ahmadexp/Open-Source-PC110/Discovery/Bowman/readme.md

# U21 "Bowman" — Detailed Analysis

*Source: `Mainboard.pdf` ("PC110 Motherboard", KiCad / Eeschema‑PDF, created 2025‑07‑20), part of the [Open‑Source‑PC110](https://github.com/ahmadexp/Open-Source-PC110) reverse‑engineering project.*

---

## 1. Summary

**U21 (value field: `Bowman`)** is the IBM PC110's **main system‑controller ASIC** — a ~144‑pin custom gate array that bridges the 80486SX CPU local bus to a 16‑bit ISA‑style system bus and absorbs nearly all of the machine's glue logic (ROM decode, interrupt aggregation, DMA handshaking, floppy, keyboard‑MCU link, audio glue and power sequencing).

This corresponds to the documented **custom RIOS chip that "controlled the ISA bus and expanded the bus width to 16 bits."** The PC110 was co‑developed by **IBM Japan and Ricoh (RIOS)** in 1995; its 486SX‑33 CPU and several support chips carry RIOS markings. `Bowman` is the project/codename used on the schematic — there is no public datasheet for the part.
The package is in fact **laser‑marked `RIOS BOWMAN 63G33 1017 JAPAN S536AAI`** (144‑QFP; see the close‑up
in [Chipset/ML-bus-payload-probe.md](../Chipset/ML-bus-payload-probe.md)) — so "BOWMAN" is a genuine part
marking, carrying an IBM `63G33`‑series part number and a `S536AAI` date/lot code, not merely a schematic codename.

| Attribute | Value |
|---|---|
| Reference designator | **U21** |
| Value / codename | **Bowman** |
| Function | System controller / CPU‑to‑ISA bridge ("chipset") |
| Pin count | 144 (highest pin = 144; QFP‑class custom gate array) |
| CPU interface | 80486SX local bus (U76, 80486SX‑33, BGA256) |
| Companion controller | U35 **"Pluto"** (linked via `Bowman_IO1/2`, `Pluto_IO`) |

---

## 2. Role in the system architecture

The PC110 is built around a small set of custom RIOS chips rather than an off‑the‑shelf chipset. Bowman is the heart of that arrangement:

```
   80486SX-33 (U76, BGA256)
        │  CPUA2..25, CPU_ADS#/MIO#/DC#/WR#/RDY#/INTR/RESET, CPUCLK
        ▼
   ┌─────────────┐    M38_IO1..12     ┌──────────────┐
   │  U21 BOWMAN │◄──────────────────►│ U67 M38813M4 │ keyboard / PM MCU
   │  (system    │                    └──────────────┘
   │  controller)│    ESS_IRQ/DACK    ┌──────────────┐
   │             │◄──────────────────►│ ES488 audio  │ (Sound Blaster)
   │             │    ROMA/ROMCE#     ┌──────────────┐
   │             │◄──────────────────►│ Flash BIOS   │
   │             │    Pluto_IO,       └──────────────┘
   │             │    Chipset_IO      ┌──────────────┐
   │             │◄──────────────────►│ U35 PLUTO    │ I/O controller
   └─────┬───────┘                    └──────────────┘
         │ SA0..15 / SD0..7 / IOR#/IOW#/AEN / IRQ2..15 / DRQ/DACK
         ▼
   16-bit ISA-style system bus  → CompactFlash, PCMCIA, YM3812 (OPL2), etc.
```

In short, the CPU talks only to Bowman on its fast local bus; Bowman translates those cycles into 16‑bit ISA bus cycles and routes interrupts, DMA, ROM and peripheral chip‑selects. The companion chip **Pluto (U35)** handles the lower‑speed/peripheral I/O (CF/dock detect, LCD, IrDA, RS‑232 enable, floppy data lines, keyboard speaker, RAM ID, BIOS write‑enable), and the two custom chips exchange status over dedicated `Bowman_IO`/`Pluto_IO` lines.

---

## 3. Complete pinout (by function)

### 3.1 CPU local bus — 80486SX interface (left side of symbol)

| Signal | Pin | Notes |
|---|---|---|
| `CPUA2`–`CPUA25` | 10‑17, 19‑27, 29‑35 | CPU address bus (A0/A1 handled as byte‑enables, not exposed here) |
| `CPU_ADS#` | 49 | Address strobe (486 ADS#) |
| `CPU_MIO#` | 50 | Memory / IO# (486 M/IO#) |
| `CPU_DC#` | 41 | Data / Control# (486 D/C#) |
| `CPU_WR#` | 42 | Write / Read# (486 W/R#) |
| `CPU_RDY#` | 134 | Ready / cycle complete (486 RDY#) |
| `CPU_INTR` | 133 | Maskable interrupt to CPU (8259 INTR equivalent) |
| `CPU_RESET` | 46 | CPU reset |
| `CPUCLK` | 38 | CPU clock |

### 3.2 16‑bit ISA‑style system bus

| Signal | Pin | Notes |
|---|---|---|
| `SA0`–`SA15` | 55‑63, 65‑71 | System address bus |
| `SD0`–`SD7` | 96,95,94,93,92,91,89,88 | System data (low byte on Bowman; high byte routed elsewhere) |
| `IOR#` | 112 | I/O read |
| `IOW#` | 113 | I/O write |
| `AEN` | 114 | Address enable (DMA in progress) |
| `MEMCS16#` | 119 | 16‑bit memory chip‑select |
| `LDEV#` | 43 | Local device select |
| `ADDHI` | 124 | High‑address qualifier |
| `DS3#` | 123 | Decode/strobe |

### 3.3 Interrupt controller (8259‑class aggregation)

| Signal | Pin | | Signal | Pin |
|---|---|---|---|---|
| `IRQ2` | 87 | | `IRQ10` | 78 |
| `IRQ3` | 85 | | `IRQ11` | 77 |
| `IRQ4` | 84 | | `IRQ12` | 76 |
| `IRQ5` | 83 | | `IRQ14` | 75 |
| `IRQ7` | 81 | | `IRQ15` | 74 |
| `IRQ9` | 79 | | `KB_IRQ1` | 86 (keyboard IRQ1) |
| `ESS_IRQ1` | 118 | | | |

### 3.4 DMA & floppy

| Signal | Pin | Notes |
|---|---|---|
| `FINTR` | 82 | Floppy interrupt |
| `FDRQ` | 115 | Floppy DMA request |
| `PDRQ` | 117 | Peripheral DMA request |
| `DACK#` | 120 | DMA acknowledge |
| `PDACK#` | 121 | Peripheral DMA acknowledge |
| `ESS_DACK#` | 122 | Audio (ESS) DMA acknowledge |
| `FDD_IO` | 125 | Floppy control I/O |

### 3.5 ROM / BIOS decode

| Signal | Pin | Notes |
|---|---|---|
| `ROMA12`–`ROMA19` | 9,7,6,5,4,3,2,143 | ROM high address lines |
| `ROMCE#` | 142 | ROM chip‑enable |

### 3.6 Keyboard / power‑management MCU (U67 = Mitsubishi M38813M4) — mapped from the schematic

> **Correction (2026‑07, from the U67 schematic sheet + KBC firmware):** the earlier claim that
> `M38_IO1..12` is a "parallel link to U67" is **wrong**. Read directly from the U67 schematic
> (`Components/U67-M38813E4HP/M38813M4.png`, IC79 = M38813 M4‑084HP, TQFP‑64), **U67 has no `M38_IO`
> pins at all.** Its entire host interface is a **classic 8042‑style keyboard‑controller bus** on the
> shared system `SD`/control lines. The `M38_IO1..12` nets on Bowman pins 97,98,101–107,110,111,139
> therefore do **not** reach U67. **A deterministic wire trace of `ASIC.kicad_sch` confirms the far end
> is U6 (the M38223 power MCU):** Bowman pins 106/107/110/111 carry U6's own port nets `M38_P15_Buf`,
> `M38_P14_Buf`, `M38_P43`, `M38_P41` (P14/P15 buffered en route; all present on U6's sheet
> `Power.kicad_sch`). So `M38_IO*` is a **narrow ~4‑line control/handshake link from U6 to Bowman**: only U6 pins P14, P15
> (buffered), P41, P43 actually reach Bowman (106/107/110/111) — the other `M38_IO` symbol pins (97–105)
> are unconnected stubs and pin 139/"IO13" is a power tie (R349→PNET1) in this schematic. So despite the
> "IO1..13" pin names it is **not** a byte‑wide bus, and **not** the `0xEC/0xED` path — that window is the
> VL82C420 chipset shadow/cache/ROM config bank ([Chipset §13j.5](../Chipset/readme.md)). U6's own
> battery/power telemetry leaves U6 over its SIO1 **serial** (→ U72 = HD151015), surfaced to software via
> APM `INT 15h 530A`. **[C]**

**U67 ↔ Bowman / Pluto — the real links** (net names from the U67 schematic; gate‑array pin numbers
from the ES488 netlist, `Discovery/ES488/mainboard.txt`):

| Signal | U67 pin (port) | Dir | Bowman pin | Pluto pin | Function | Conf |
|---|---|---|---|---|---|---|
| `SD0`–`SD7` | 3,2,1,64,63,62,61,60 (DQ0‑7) | I/O | shared SD bus | shared SD bus | 8‑bit host/system data bus (DBB) | **[C]** |
| `IOW#` | 4 (W#) | in | 113 | 89 | host I/O write strobe | [C] net / [H] pins |
| `IOR#` | 5 (R#) | in | 112 | 86 | host I/O read strobe | [C] net / [H] pins |
| `KBCCS#` | 6 (S#) | in | — | 60 | KBC chip‑select (Pluto decodes the I/O port) | **[C]** |
| `SA[2]` (A0) | 7 (A0) | in | — | — | register / command‑vs‑data select (ISA A2) | **[C]** |
| `IRQ1` | 15 (P44) | out | 86 | — | keyboard interrupt to host | **[C]** |
| `IRQ12` | 14 (P45) | out | 76 | — | mouse/aux interrupt to host | **[C]** |
| `KB_CNTR#` | 59 (P60/CNTR#) | — | — | 61 | control/counter line to Pluto (via R494) | [C] net / [H] dir |
| `SPKUP` | 29 (P23) | out | — | 44 | speaker drive (up) | **[C]** |
| `SPKDN` | 30 (P22) | out | — | 43 | speaker drive (down) | **[C]** |
| `RESET#` (`RSTDRV#`) | 19 | in | 48 | 66 | system reset (multi‑drop, from IC106) | **[C]** |
| `KBRST#` | 10 (P51/TXD) | out | (sheet 009) | — | KBC→CPU fast reset (8042 output) | **[C]** |
| `A20G` | 11 (P50/RXD) | out | (sheet 009) | — | A20 gate (8042 output) | **[C]** |

`KB_SCRLED#` on **Bowman 53** is *not* U67's scroll‑lock LED: the schematic shows U67's `SCRLED#`
(pin 25) going to the LED sub‑board (sheet 023), so Bowman‑53's net is a separate/derived signal. **[H]**

**Full U67 (M38813M4) pinout** and the 8042 host protocol are documented in the Pluto readme
(§ "M38813 keyboard/PM MCU — full pinout"), since Pluto is the chip that chip‑selects and gates it.

### 3.7 Power, clocks & housekeeping

| Signal | Pin | Notes |
|---|---|---|
| `PWRGD_IN` | 141 | Power‑good input from PSU |
| `PWRGD` | 47 | Power‑good output / system ready |
| `PSU_IO1` / `PSU_IO2` | 131 / 138 | Power‑supply control I/O |
| `24MHz` | 40 | 24 MHz reference clock |
| `32kHz` | 51 | 32.768 kHz timekeeping clock |
| `VolUP` / `VolDN` | 127 / 128 | Volume button inputs |
| `Pluto_IO` | 129 | Link to U35 (Pluto) |
| `Chipset_IO1`–`5` | 45,140,39,52,130 | **VL82C420↔Bowman ML bus** (measured live 2026-07-06, pin IDs corrected 2026-07-14, see [Chipset §11b](../Chipset/readme.md)): `Chipset_IO3`/pin 39 = **MLCLK** (~22.7 MHz), `Chipset_IO4`/pin 52 = **MLADS#**; `Chipset_IO1/2/5` (45/140/130) idle = **MLRDY#/MLLBA#/MPriority** (adopted naming, in KiCad; cache-less / fixed-timing) |

### 3.8 Power rails

| Rail | Pins |
|---|---|
| `VCC` / `VCC2` | 1, 18, 36, 37, 54, 72, 73, 90, 99, 108, 109, 126, 144 |
| `GND` | 8, 28, 44, 64, 80, 100, 116, 136 |
| `NC` (no connect) | 132, 135, 137 |

---

## 4. Surrounding components and the chips Bowman talks to

| Ref | Part | Role | Link to Bowman |
|---|---|---|---|
| **U76** | 80486SX‑33 (BGA256) | Main CPU (Intel SL‑Enhanced, RIOS‑marked) | CPU local bus + control |
| **U35** | **Pluto** (custom, ~100‑pin) | Peripheral I/O controller (CF/dock/LCD/IrDA/RS‑232, FDD data, KB speaker, RAM ID, BIOS WE) | `Bowman_IO1/2`, `Pluto_IO`, shared SA/SD bus |
| **U67** | M38813 / M38813M4 | Mitsubishi 740‑family keyboard MCU (8042‑style KBC) | 8042 host bus (`SD0‑7`,`IOR#`/`IOW#`,`KBCCS#`,`SA2`), `IRQ1`(pin15→B86), `IRQ12`(pin14→B76), `RESET#`(19). **NOT** `M38_IO*` (see §3.6) |
| **U10** | YM3812 (OPL2) + YM3014B DAC | Yamaha FM synthesis | via ISA bus |
| — | ES488 / ES488F | ESS AudioDrive (Sound‑Blaster‑compatible) | `ESS_IRQ1`, `ESS_DACK#` |
| — | Flash BIOS ROM | System firmware | `ROMA*`, `ROMCE#` |
| **J11** | CompactFlash | Mass storage (16‑bit `SD0..15`) | via ISA bus |
| **U70** | TPS2201 | PCMCIA dual‑slot power switch (near U21) | PSU / PNET nets |
| **U30A** | 74LVT74 | Flip‑flop / reset timing near U21 | PNET nets |

Local support around U21 on the sheet includes pull‑ups `R98` (4.7k) / `R99` (470Ω), transistors `Q9` / `Q13`, and the `PNET`/`PSU_IO` power‑sequencing network shared with the PCMCIA power switch — consistent with Bowman also overseeing card‑slot power‑up and reset timing.

---

## 5. Observations & open questions for the project

1. **No `CPUA0`/`CPUA1`.** The CPU address bus to Bowman starts at A2; byte selection is presumably handled via byte‑enable signals (standard for the 486 bus). Worth confirming which pins carry BE# if any.
2. **8‑bit data on Bowman, 16‑bit elsewhere.** Bowman exposes only `SD0..7`, yet the documented job of the RIOS chip is the **16‑bit** bus expansion (CompactFlash uses `SD0..15`). The high byte / `MEMCS16#` steering likely happens through `ADDHI`, `Chipset_IO*`, or in concert with Pluto — a good thing to trace against the X‑rays.
3. **Bowman ↔ Pluto coupling (traced 2026‑07).** The dedicated inter‑gate‑array link is a **single
   point‑to‑point line**: Bowman **pin 129 `Pluto_IO`** ↔ Pluto **pin 51 `Bowman_IO1`** (direct, no series
   R). Pluto's **pin 52 `Bowman_IO2`** is **not wired to Bowman** — it dead‑ends on the ASIC sheet
   (effectively NC/spare; the earlier "R85" note is unverified — R85 is absent from `ASIC.kicad_sch`).
   Beyond that one wire the two chips share only standard ISA/system control: `AEN` (U21‑114↔U35‑6),
   `IOR#` (112↔86), `IOW#` (113↔89), `KB_RESET#` (48↔66), `PWRGD` (47↔67). The lone `Pluto_IO`/`Bowman_IO1`
   line is an inter‑gate‑array **status/handshake** signal; its direction and protocol aren't determinable
   from connectivity alone (one wire, no software‑visible register — would need a live bus probe). **[C]**
   connectivity / **[H]** function.
4. **Codenames.** ~~`Bowman` and `Pluto` appear to be project codenames rather than IBM/RIOS part markings.~~ **Partly resolved (2026-07-14):** the Bowman package is laser‑marked `RIOS BOWMAN 63G33 1017 JAPAN S536AAI`, so `BOWMAN` *is* the real part marking (IBM `63G33`‑series P/N). Whether `Pluto` is likewise marked on U35 is still open.

### Live probe (2026) — Bowman has no host-readable config bank ✅ **[RE]**
Bowman is the **transparent 486↔ISA bridge**: unlike the VL82C420 (which has an indexed config space
now dumped — see [Chipset §13a](../Chipset/)) and Pluto (whose FDC/PCIC/EC windows are readable — see
[Pluto §6c](../Pluto/)), Bowman does **not** expose a host-visible register bank. Live probing on a
running unit found the two candidate config-pair banks the BIOS helper table can reach —
`0x24/0x25` and `0xD00/0xD01` — read back **all-`0xFF`** on this machine (even with the `0x22/0x23`
config gate open), and the `0x4F` config latch Bowman/SCAMP shares is **write-only** (147 POST writes,
zero reads; indices `0x11,0x66,0x70,0x0A,0x1E,0xB6,0x8F,0x65,0xBF,0xFF`). So Bowman's bridge/decode
behaviour is configured at POST and is not read-back-able at runtime — consistent with a hard-wired
gate array rather than a programmable controller with a live register file.

---

---

## 6. Discovery from the ROM dump — U36 font ROM (`MSM538032E@SOP44.BIN`)

A binary dump was supplied as "from U28," but U28 in the schematic is DRAM (`M5M4V16160BTP`). The dump actually belongs to **U36**, the OKI **`MSM538032E`** mask ROM (alt. marking `M538032C`, SOP‑44, 16‑bit `D0..D15`, `A0..A19`, `CE#`/`OE#`/`BHE`, on the `OKI_SA*` / `SD[0..15]` nets). Its address/select interface **is** Bowman's `ROMA*`/`ROMCE#` bus (see "How the CPU reads it" below); the **BIOS flash** (U59, 28F002) is decoded *separately* by the **chipset** (`Chipset_BIOS_CE#`), so the two ROMs do **not** share a chip‑select. This is a CPU‑addressable **font ROM** on the system data bus.

### What the dump contains

- **Header:** magic `55 AA 10 CB`, label `FONT`, and the string
  `84G7940 (C) Copyright IBM Corporation 1990, 1995 All Rights Reserved`, dated **03/23/95**.
- **IBM part number 84G7940** — the PC110 **DOS/V display font ROM**.
- Size **1 MiB**; the file is fully populated (the seven font regions account for ~1 MB).

### Font directory (parsed from offset 0x210; 48‑byte entries)

| Font set | Glyph size | Bytes/glyph | Data offset | Glyphs |
|---|---|---|---|---|
| System SBCS 12 | 6 × 12 | 12 | 0x0D8000 | 256 |
| System SBCS 16 | 8 × 16 | 16 | 0x002000 | 256 |
| System SBCS 19 | 8 × 19 | 19 | 0x000400 | ~256 |
| System SBCS 24 | 12 × 24 | 48 | 0x044000 | 256 |
| System DBCS 12 | 12 × 12 | 18 | 0x0D8C00 | ~8,900 |
| System DBCS 16 | 16 × 16 | 32 | 0x003000 | ~8,300 |
| System DBCS 24 | 24 × 24 | 72 | 0x047000 | ~8,200 |

- **SBCS = single‑byte (ANK), JIS X 0201:** ASCII (with `¥` at 0x5C instead of backslash) plus half‑width katakana at 0xA1–0xDF. Rendering glyph 0x41/0x42 produces a clean "A"/"B" — confirmed.
- **DBCS = double‑byte, JIS X 0208:** hiragana, full‑width katakana, Greek, Cyrillic, symbols, and the ~6,800 kanji of JIS levels 1 & 2. Rendered glyph blocks show correct kana/Greek/Cyrillic.

### Why it matters

The PC110 has no hardware kanji video; **IBM DOS/V renders Japanese text in software by reading bitmaps from this ROM.** Four pixel heights (12/16/19/24) supply screen text, larger UI, and print‑quality glyphs. Decoding the directory format means the entire glyph set can now be extracted, documented, and cross‑checked — useful for a full BOM entry on U36 and for anyone re‑implementing the font path (e.g., in an FPGA or emulator).

Render proofs: `font_SBCS16_ascii.png` (single‑byte set) and `font_DBCS16_kanji.png` (double‑byte kana/Greek/Cyrillic block).

### How the CPU reads it — decode & paging  ✅ **[C, from `ROM.kicad_sch` + datasheet]**

Traced deterministically from `PCB/Mainboard/ROM.kicad_sch`:

| U36 pins | Net | Source |
|---|---|---|
| A0–A11 (low addr) | `SA1`–`SA12` | **direct ISA system address** — the access *window* |
| A12–A19 (high addr) | `OKI_SA12`–`OKI_SA19` = Bowman `ROMA12`–`ROMA19` | **Bowman page latch** (8 bits) |
| CE# | `OKI_CE#` = Bowman `ROMCE#` (pin 142) | Bowman address decode |
| OE# | `MEMR#` | ISA memory‑read → a **memory** window, not I/O |

So the 1 MiB font ROM is a **paged, memory‑mapped ROM controlled by Bowman**: the CPU sees a small window
addressed directly by the ISA bus (`SA1–SA12`), and Bowman supplies the upper address (page) via its
`ROMA12–19` latch — the CPU selects a page by writing a Bowman register, then reads glyph data from the
window. **Page 0 is an 8 KB option‑ROM window** (the `55 AA 10 CB` header at offset 0, size byte `0x10` =
8192 bytes, checksum‑valid) — exactly the `SA1–SA12` span, and the DOS/V font driver's entry point.

**This corrects §6's opening (and §3.5):** Bowman's `ROMA*`/`ROMCE#` drives the **font ROM (U36)**, *not*
the BIOS flash. The BIOS flash (U59, 28F002BX) is a **chipset‑decoded** path (`Chipset_BIOS_CE#`,
`Chipset_SA16`, `BIOS_SA17`, `OE#=MEMR#`) — a separate select; the two ROMs never share a chip‑enable.

### Open items — resolved
- **Second bank? No.** The MSM538032E is an **8‑Mbit (1 MiB)** part — 512 K × 16 / 1 M × 8 (datasheet
  `Datasheets/top/MSM538032C.pdf`; analysis report: "8‑Mbit mask ROM, 1 MiB as x8"). The 1 MiB dump is the
  **complete device** — no second bank. (The earlier "~2 MB / A0–A19×16" worry assumed word‑wide use of
  all 20 lines; the device is 8 Mbit.)
- **`OKI_SA*`/`OKI_CE#` decode: mapped above** — Bowman‑paged, memory‑mapped (`ROMA12–19` page latch +
  `SA1–12` window + `ROMCE#`/`MEMR#`).

---

## Sources

- Uploaded schematic: `Mainboard.pdf` ("PC110 Motherboard", KiCad).
- Uploaded ROM dump: `MSM538032E@SOP44.BIN` (IBM font ROM P/N 84G7940, 1995).
- [Open‑Source‑PC110 (GitHub) — ahmadexp](https://github.com/ahmadexp/Open-Source-PC110)
- [Reverse Engineering The IBM PC110, One PCB At A Time — Hackaday](https://hackaday.com/2025/04/06/reverse-engineering-the-ibm-pc110-one-pcb-at-a-time/)
- [IBM PalmTop PC110 teardown — iPhone Wired](https://iphonewired.com/news/11094/) (CPU 486SX‑33 BGA with RIOS markings; C&T 65535A graphics; ESS + Yamaha audio; IBM Japan + Ricoh)
- [PC110 — ThinkWiki](https://www.thinkwiki.org/wiki/PC110)
