ahmadexp/Open-Source-PC110/Discovery/Trackpoint/readme.md

# U75 — Trackpad Controller

*PC110 Motherboard · KiCad reverse-engineering project (Open-Source-PC110)*

---

## 1. Summary

**U75** is the **trackpad (pointing-device) controller** on the IBM PC110 motherboard. Instead of a dedicated touch ASIC, the design uses a small general-purpose **4-bit microcontroller** running firmware that scans the capacitive/resistive pad matrix, reads the physical click buttons, and reports pointer movement to the host over a PS/2-style clock + data interface.

| Field | Value |
|---|---|
| Reference designator | **U75** |
| Part number (Value) | **D17137AGT** (NEC µPD17137A) |
| Device class | 4-bit single-chip microcontroller (NEC "17K" / µPD17134A subseries) |
| Footprint | **PC110:SSOP-28** (28-pin shrink small-outline package) |
| Schematic description | "Trackpad Controller" |
| Net-naming prefix | `D171_` (derived from the part number) |
| Source document | `Mainboard.pdf` — *PC110 Motherboard*, generated by KiCad Eeschema |

---

## 2. The part: NEC µPD17137A

`D17137AGT` decodes to NEC's **µPD17137A**, a member of the **µPD17134A subseries** of NEC's **17K-family 4-bit single-chip microcontrollers** (circa early 1990s). The leading `D` is NEC's standard prefix (µPD), and the `GT` suffix denotes the package option.

Key characteristics of the family:

- 4-bit CMOS single-chip microcontroller architecture.
- On-chip ROM/RAM, timer, and general-purpose I/O ports organized into nibble-wide ports (P0A, P0B, P0C, P1A, P1B …).
- Designed for low-cost embedded control tasks — exactly the role it plays here, scanning a pointing-device sensor and emulating a mouse.

Using a programmable MCU (rather than fixed-function silicon) is why the schematic exposes raw port lines (`P0A0`, `P0B1`, etc.) directly to the pad — the scanning logic lives in firmware.

---

## 3. Connections / net map

All I/O nets carry the `D171_` prefix (after the part number). Grouped by function:

### Pad sensing matrix (scan / sense lines)
These read finger position off the trackpad surface.

- **Port 0A:** `/D171_P0A0`, `/D171_P0A1`, `/D171_P0A2`, `/D171_P0A3`
- **Port 0B:** `/D171_P0B0`, `/D171_P0B1`, `/D171_P0B2`, `/D171_P0B3`
- **Port 0C:** `/D171_P0C2`, `/D171_P0C3`
- **Port 1A:** `/D171_P1A0`, `/D171_P1A1`, `/D171_P1A2`, `/D171_P1A3`
- **Port 1B:** `P1B0` (appears as the auto-named net `Net-(U75-P1B0)`)

### Button inputs
- `/TRKPD_Lclick` — left physical click button
- `/TRKPD_Rclick` — right physical click button

### Host interface (pointer data out)
- `/D171_GPCLK` — PS/2-style clock line
- `/D171_GPDATA` — PS/2-style data line

### Control
- `Net-(U75-INT)` — interrupt line

### Power
- **`PNET3`** — supply rail
- **`GND`** — ground

---

## 4. Support circuitry around U75

### Decoupling / bulk capacitors
| Ref | Value | Footprint |
|---|---|---|
| C87 | 120 nF | C_0402_1005Metric |
| C126 | 150 nF | C_0402_1005Metric |
| C135 | 2.7 µF | C_0805_2012Metric |

### Resistors (pull-ups / dividers)
| Ref | Value | Notes |
|---|---|---|
| R196 | 47 k | |
| R197 | 47 k | |
| R198 | 10 k | |
| R200 | 47 k | |
| R201 | 100 k | |
| R203 | 10 k | |
| R204 | 47 k | |
| R205 | 100 k | |
| R206 | 47 k | |
| R199 | DNP | not populated |
| R202 | DNP | not populated |

All resistors use the `R_0402_1005Metric` footprint.

---

## 5. Board neighborhood

U75 sits in a dense region of the motherboard alongside the core system controllers, and the CPU data bus (`/CPU_D28`–`/CPU_D31`) routes nearby.

| Ref | Value | Role | Package |
|---|---|---|---|
| **U51** | CHIPS65535 | Chips & Technologies VGA / LCD controller | BGA-169 |
| **U74** | RB5C396 | Ricoh PC-Card / power controller | BGA-256 |
| **U75** | D17137AGT | Trackpad controller | SSOP-28 |

Other nearby nets observed: `Net-(C135-+)`, `Net-(C281--)`, `Net-(C283-+)`, and power net `PNET3`.

---

## 6. Functional picture

```
                 +-------------------------+
  Pad matrix --->|  P0A0..P0A3             |
  (rows/cols)    |  P0B0..P0B3             |
                 |  P0C2, P0C3             |
                 |  P1A0..P1A3, P1B0       |
                 |                         |
  L/R buttons -->|  TRKPD_Lclick           |---> GPCLK  (PS/2 clock) --> host KBC
                 |  TRKPD_Rclick           |---> GPDATA (PS/2 data)  --> host KBC
                 |                         |
                 |  U75  (NEC uPD17137A)   |---> INT (interrupt)
                 |  SSOP-28, 4-bit MCU     |
                 +-----------+-------------+
                       PNET3 |  | GND
                             |  |
                        decoupling: C87, C126, C135
```

The MCU continuously drives/reads the port lines to scan the pad, debounces the two click inputs, and streams the resulting pointer packets to the system's keyboard/mouse controller over the `GPCLK`/`GPDATA` pair.

---

## 7a. Live probe & firmware-extraction feasibility (2026)  ✅ **[RE]**

**Question asked:** can U75's firmware be dumped *from inside* — i.e. over the running system
([COMrade](../Live-Dump/)), without desoldering/decapping? Investigated live; the short answer is
**no**, and here is exactly why, with on-device evidence.

**U75 is reachable, and it is alive.** Its only host path is the **PS/2 aux channel** through the
8042 keyboard controller (the `GPCLK`/`GPDATA` pair, §3). On a running unit that channel is
**disabled at rest** (8042 command byte `0x65`: aux-disable bit set, IRQ12 off — no mouse driver
loaded at the DOS prompt). Bringing it up (`0xA8`), querying the device, and restoring the byte to
`0x65` afterwards, U75 answers the standard pointing-device protocol perfectly:

| Command | Response | Meaning |
|---|---|---|
| Reset `0xFF` | `FA AA 00` | ACK, **self-test passed (BAT OK)**, device ID `0x00` |
| Get device ID `0xF2` | `FA 00` | **standard PS/2 mouse** (no wheel/5-button extension) |
| Status request `0xE9` | `FA 00 02 64` | stream mode, reporting off, **resolution 4 counts/mm**, **sample rate 100/s** |

**Why the firmware can't come out this way.** That table is the *entire* host-visible surface of
U75. The PS/2 pointing-device command set (reset, identify, set/get sample-rate, set/get resolution,
set scaling, stream/remote/wrap modes, read-data) has **no memory- or ROM-read command** — by design
it only moves pointer packets and config. Underneath:

1. **Separate MCU, internal mask ROM.** The µPD17137A executes from on-chip **mask ROM** that lives
   only on the 4-bit core's internal bus. It is **not memory-mapped** to the 486 — there is no
   address/data path from the host into U75's program store.
2. **Mask ROM ≠ OTP.** In-system serial verify/readback exists on the **OTP/EPROM** sibling
   (`µPD17P137A`) and only in a **programmer socket** via dedicated pins — not during normal
   operation, and not on the mask `µPD17137A` fitted here.
3. **No external ROM to sniff.** The net map (§3) shows pad-sense ports, the PS/2 pair, INT and
   power — there is **no external ROM/EEPROM** and no host-driven firmware upload. The code is
   permanent silicon inside U75.

**What would actually get the firmware (all offline / physical):**
- **Decap + optical read** of the mask-ROM array — a mask ROM is literally patterned in the metal/
  diffusion layer and can be imaged and decoded under a microscope (the standard route for these
  parts).
- **Delayer + SEM** imaging if the ROM is a contact/implant type that isn't optically visible.
- **Substitute an OTP `µPD17P137A`** and read it in a NEC/Renesas 17K programmer (gets *a* dump only
  if you have the same firmware to program — not the factory mask contents).

So the trackpad MCU is fully *characterised and controllable* from inside (it's a bog-standard PS/2
mouse, ID `0x00`, 4 counts/mm, 100 Hz), but its firmware is **not extractable** without die-level
work. The 8042 aux state was left exactly as found (command byte `0x65`, aux disabled).

## 7b. Pin-level extraction via the 17K PROM/verify mode — SETTLED  ❌ **[not possible on the mask part]**

Can it come out by **probing the raw device pins** (verify mode) instead of the host? The NEC µPD17134A
subseries user manual (**U11607EJ3V0UM00**, 3rd ed. 1996 — obtained 2026-07-06) answers this
**definitively: no, not on the mask µPD17137A fitted here.**

**The one-time-PROM parts DO have a full pin-level ROM readout** (Chapter 18, *One-Time PROM
Writing/Verifying*), and it is exactly the mechanism expected:

*Table 18-1 — Pins Used for Writing/Verifying Program Memory:*
| Pin | Function in program mode |
|---|---|
| `VPP` | apply **+12.5 V** |
| `VDD` | apply **+6 V** |
| `RESET` | reset input; initialises all states before entering write/verify mode |
| `CLK` | clock input for updating address — **advances the program address by inputting four pulses** |
| `MD0`–`MD3` | select operation mode |
| `D0`–`D7` | 8-bit data I/O |

*Table 18-3 — Setting Operation Modes* (with `VPP`=+12.5 V, `VDD`=+6 V): address-0-clear = `MD` `HLHL`;
write = `LHHH`; **verify = `LLHH`**; program-inhibit = `H×HH`. *Reading procedure (§18.4, Fig 18-2):*
reset → address-0-clear → set **verify** → then clock `CLK`; **"data for each address is sequentially
output, four clocks per address"** on `D0`–`D7`. (`P1B0`/`VPP` is the dual-function pin — it becomes
`VPP` in program mode.)

**But this applies ONLY to the OTP `µPD17P136A`/`17P137A`.** *Table 18-2 — Differences Between Mask ROM
Version and One-Time PROM Version* is explicit:

> **"VPP pin and operating-mode-select pin" — µPD17134A/17135A/17137A (Mask ROM): _Not available_;
> µPD17P136A/17P137A (OTP): _Provided_.**

So the mask `µPD17137A` (U75) **physically has no `VPP` pin and no `MD0`–`MD3` mode-select pins** — there
is no way to enter write/verify mode, hence **no pin-level ROM readout at all.** (This corrects the
earlier speculation that the mask part might retain a factory verify mode — it does not expose one.)

**Conclusion (final):** neither the host (§7a) nor pin-level probing/verify-mode (this section) can
extract U75's firmware. The mask ROM is only recoverable by **decap + optical/SEM die imaging** (§7a).
The OTP verify procedure above is documented for completeness / in case a `µPD17P137A` is ever imaged or
substituted.

## 7. Sources

- [Reverse Engineering The IBM PC110, One PCB At A Time — Hackaday](https://hackaday.com/2025/04/06/reverse-engineering-the-ibm-pc110-one-pcb-at-a-time/)
- [Open-Source-PC110 — GitHub](https://github.com/ahmadexp/Open-Source-PC110)
- [µPD17137A 4-bit single-chip microcontroller datasheet (NEC)](https://datasheetspdf.com/datasheet/UPD17137A.html)
- [1992 NEC 17K 4-bit Microcontroller Data Book — bitsavers.org](https://www.bitsavers.org/components/nec/_dataBooks/1992_NEC_17K_4-bit_Microcontroller_Data_Book.pdf)
- Primary source: `Mainboard.pdf` (PC110 Motherboard schematic, KiCad Eeschema export)

---

## 5. Live host-side probe (2026-07-04)

Probed U75 live over the 8042 aux channel (via COMrade port I/O; aux IRQ disabled,
data-reporting stopped, then restored). It answers standard PS/2 mouse commands:

| Command | Reply | Meaning |
|---|---|---|
| `F2` Get device ID | `FA 00` | ID **0x00** — standard PS/2 mouse |
| `E9` Status request | `FA 00 02 64` | flags `0x00`, resolution `0x02` (4 counts/mm), sample rate `0x64` (100 /s) |
| `E1` Read secondary ID | `FE` | resend → **not** IBM TrackPoint firmware |
| `E2 80 <addr>` Read RAM | `FC/FE` | error/resend → **no** IBM extended RAM registers |
| `F4` Enable reporting | `FA` | ack |

**Conclusion — the internal program (mask) ROM is NOT software-dumpable.** U75 is a
masked µPD17137A whose only host interface is the standard PS/2 mouse protocol; it
exposes no memory-read/extended command and has no external ROM bus (unlike the
font ROM). The complete software-accessible state is the ID + status above. Reading
the actual firmware would require hardware means (decap + micro-probe, or a NEC
factory test/PROM mode via the raw device pins — not reachable from the host).
