ahmadexp/Open-Source-PC110/Discovery/Inking/readme.md

# Inking / signature pad — the PC110 digitizer, reverse-engineered

The IBM PC110 has a **resistive inking pad** (a pen/handwriting/signature digitizer)
distinct from the trackpad. It is what the Japanese handwriting stack (`INKDRV.COM`,
the `IBMSMALL.DCT` / `$USRDICT.DCT` dictionaries seen in the [Live-Dump](../Live-Dump/))
draws on. Easy-Setup exposes it as **`PS2 ADDINKing`** (I/O base `15E0|25E0|35E0`) and
**`PS2 IRQINKing`** (`5|10`); the factory `D:\CONFIG.SYS` sets it up with
`RMUDOSAT.SYS /IX=5,10 /PX=15E0-15EF,35E0-35EF` (note `IX=5,10` == the two `IRQINKing`
options). See [PS2 §4](../PS2/README.md).

Physically the pad is a resistive touch panel read by the **M38223 "power-sense" MCU**
(`touch panel on P1/P6 ADC`, see [`Components/Flash/M38223E4HP`](../../Components/Flash/M38223E4HP/)),
which strobes digitized samples over a byte bus to the **Bowman** ASIC; Bowman presents
them to the CPU at the inking I/O window.

## Where it lives (this unit)

Read live over [COMrade](../../) (2026-07): CMOS `0x68` low-2 bits select the base from
`{15E0, 25E0, 35E0}`; here it is **`0x15E0`** (the `0x35E0` window reads all-`FF`).
Idle window at `0x15E0`: `00 FF C0 FF FF FF FF FF 00 FF FF FF 40 FF 80 00`, so control
(`base+2`) idles at `0xC0`, status (`base+1`) at `0xFF`. Config is persisted in CMOS
`0x68..0x6F` (standard bank via `0x70/0x71`; the driver uses the `0x74/0x76` extended
bank only for indices with bit7 set).

## Register model (base = 0x15E0)

| Port | Dir | Meaning |
|---|-----|---|
| `base+0` (`15E0`) | R | data byte (one byte of a 3-byte packet) |
| `base+1` (`15E1`) | R | status; **bit7 = a data byte is waiting** |
| `base+2` (`15E2`) | R/W | control; write `0x38` = enable reporting; pulse **bit0** to ack a byte |

**Enable → status flips.** Verified live: writing `0x38` to `base+2` changes status from
`0xFF` (disabled/floating) to `0x7F` (enabled, bit7 clear = no data). Restoring the saved
control byte disables it.

**The pad is IRQ-driven, not pollable.** In practice the digitizer delivers each byte only
by raising its interrupt — polling `base+1` bit7 never catches the data (confirmed on real
hardware: a polled reader shows nothing while signing). You must hook the inking IRQ,
enable the pad, and read `base+0` in the ISR (exactly as `INKDRV` does).

## Packet format (3 bytes)

`INKDRV.COM`'s IRQ handler reads one byte per interrupt from `base+0`, acks (`base+2`
read-modify-write: `|1` then `&~1`), and assembles **3-byte packets**:

```
byte0 = flags   (bit7 = 1, packet sync/first byte)
                 bit4 = rawX bit8
                 bit3 = rawY bit8
                 bit0 = pen-down (tip switch)
byte1 = rawX low 7 bits
byte2 = rawY low 7 bits

rawX = byte1[0..6] | (flags.bit4 << 7)      ; 0..255
rawY = byte2[0..6] | (flags.bit3 << 7)      ; 0..255
```

Only `byte0` has bit7 set, so `byte1/byte2` carry 7 bits each and the 8th bit rides in the
flags byte. `INKDRV` then maps raw → screen with a **4-point calibration** ("Touch the
left-up / right-up / left-down / right-down corner of inking pad") stored in CMOS; its
uncalibrated defaults are X range `0xF9` (249), Y range `0x81` (129), origins 0.

## Driver interface (`INKDRV.COM`, "Inking Low Level Driver v1.00, (C) 1995 RIOS Systems")

- Reads base/IRQ via the PC110 APM vendor call `INT 15h AX=5380, BX=8300` → `CL`:
  `CL & 3` indexes the base table `{05E0, 15E0, 25E0, 35E0}`; `(CL & 0x70) >> 4` indexes
  the IRQ table `{3,4,10,11,12,15,5,7}` (vector = IRQ+8, +0x60 more for the slave PIC).
- Hooks the inking IRQ vector directly (ISR at its own `+0xF8`), rings incoming bytes,
  and delivers assembled samples to an app callback registered via `INT 15h AX=5403`
  (with `5402/5407` for arbitration). Also usable through its **INT 51h** entry.
- `INKDRV /C` recalibrates; `INKDRV /R` removes.

## In PS2GUI

[`Software/PS2GUI`](../../Software/PS2GUI/) adds a **System Test → "Signature pad test"**
that drives the pad directly (no resident driver needed): read base + IRQ via
`INT 15h 5380/8300`, hook the inking IRQ vector, unmask it in the PIC, enable the pad
(`out base+2,0x38`), and let a small ISR read `base+0` + ack (`base+2` bit0 pulse) into a
ring buffer. The main loop drains the ring, assembles 3-byte packets, and draws the pen
strokes in a VGA (mode 12h) signing box with a live raw X/Y/pen/packet readout. On exit it
disables the pad and restores the IRQ vector + PIC mask. Confirmed on real hardware: the
pad reports and the signature draws.

## Confidence

- ✅ **Hardware-confirmed**: the IRQ-driven path reports live pen data and draws the
  signature on a real PC110 (base `0x15E0`, IRQ per `INT 15h 5380/8300`).
- ✅ **Verified live over COMrade**: base `0x15E0` on this unit, the `0x38` enable flipping
  status `0xFF→0x7F`, restore, and the CMOS `0x68` base selector.
- ✅ **From disassembly** of the unit's `D:\INKDRV.COM`: the register handshake, the
  3-byte packet + flag-bit layout, calibration scaling, base/IRQ tables, and the
  `INT 15h 53/54xx` + `INT 51h` interfaces.
- ✅ **Calibrated**: the PS2GUI test has its own **4-corner calibration** (press `C`, touch each
  pad corner); it fits a linear raw→screen map (left/right/top/bottom raw averages), clamps into the
  measured range, and handles a flipped axis, so strokes land accurately. (Held in RAM for the
  session; it does not yet persist to CMOS the way INKDRV's calibration does.)
