ahmadexp/Open-Source-PC110/Discovery/ES488/u4_region.png

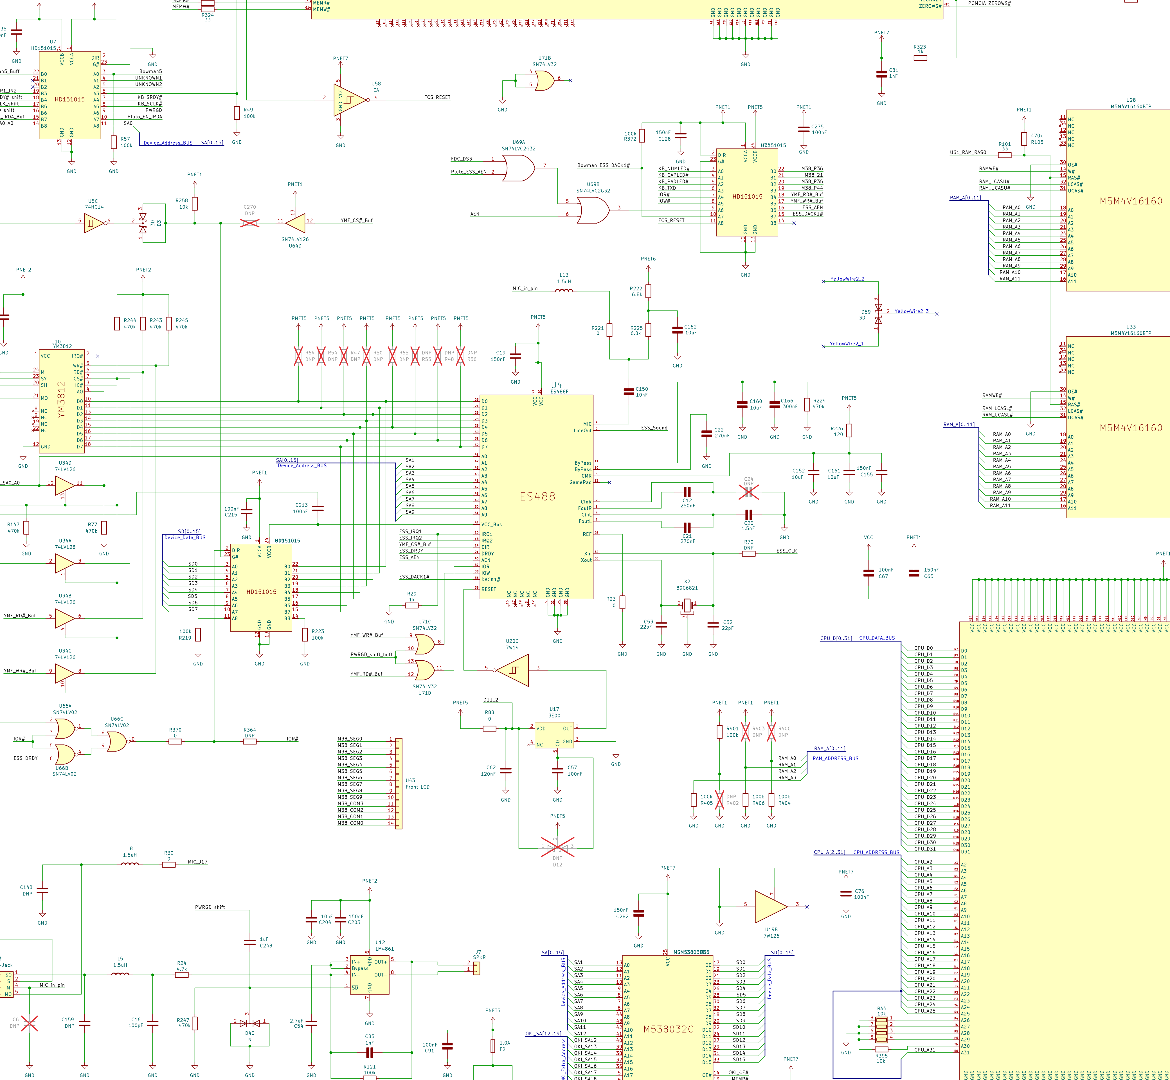
Discovery/ES488/u4_region.png
