ahmadexp/Open-Source-PC110/Discovery/Pluto/u35_bot2.png

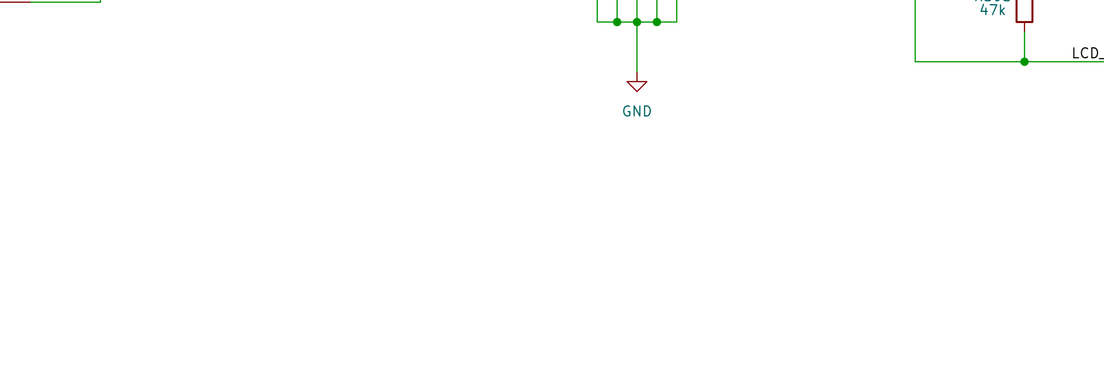
Discovery/Pluto/u35_bot2.png
