ahmadexp/Open-Source-PC110/Discovery/Pluto/u35_bottom.png

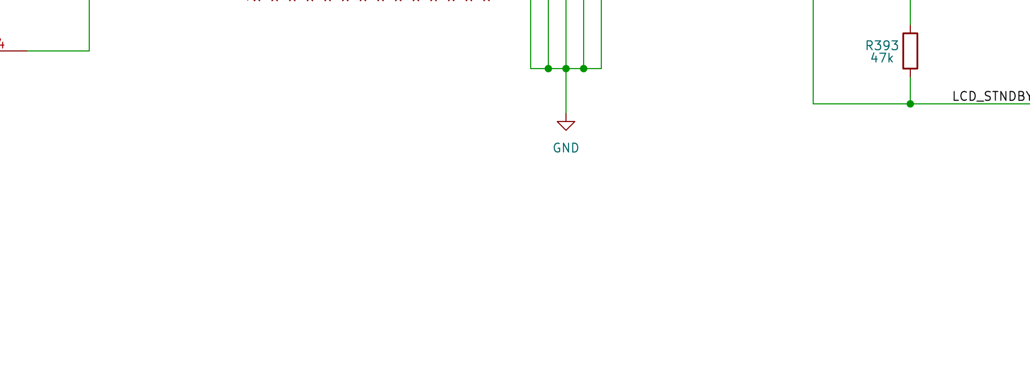
Discovery/Pluto/u35_bottom.png
