ahmadexp/Open-Source-PC110/Discovery/Pluto/u35_left.png

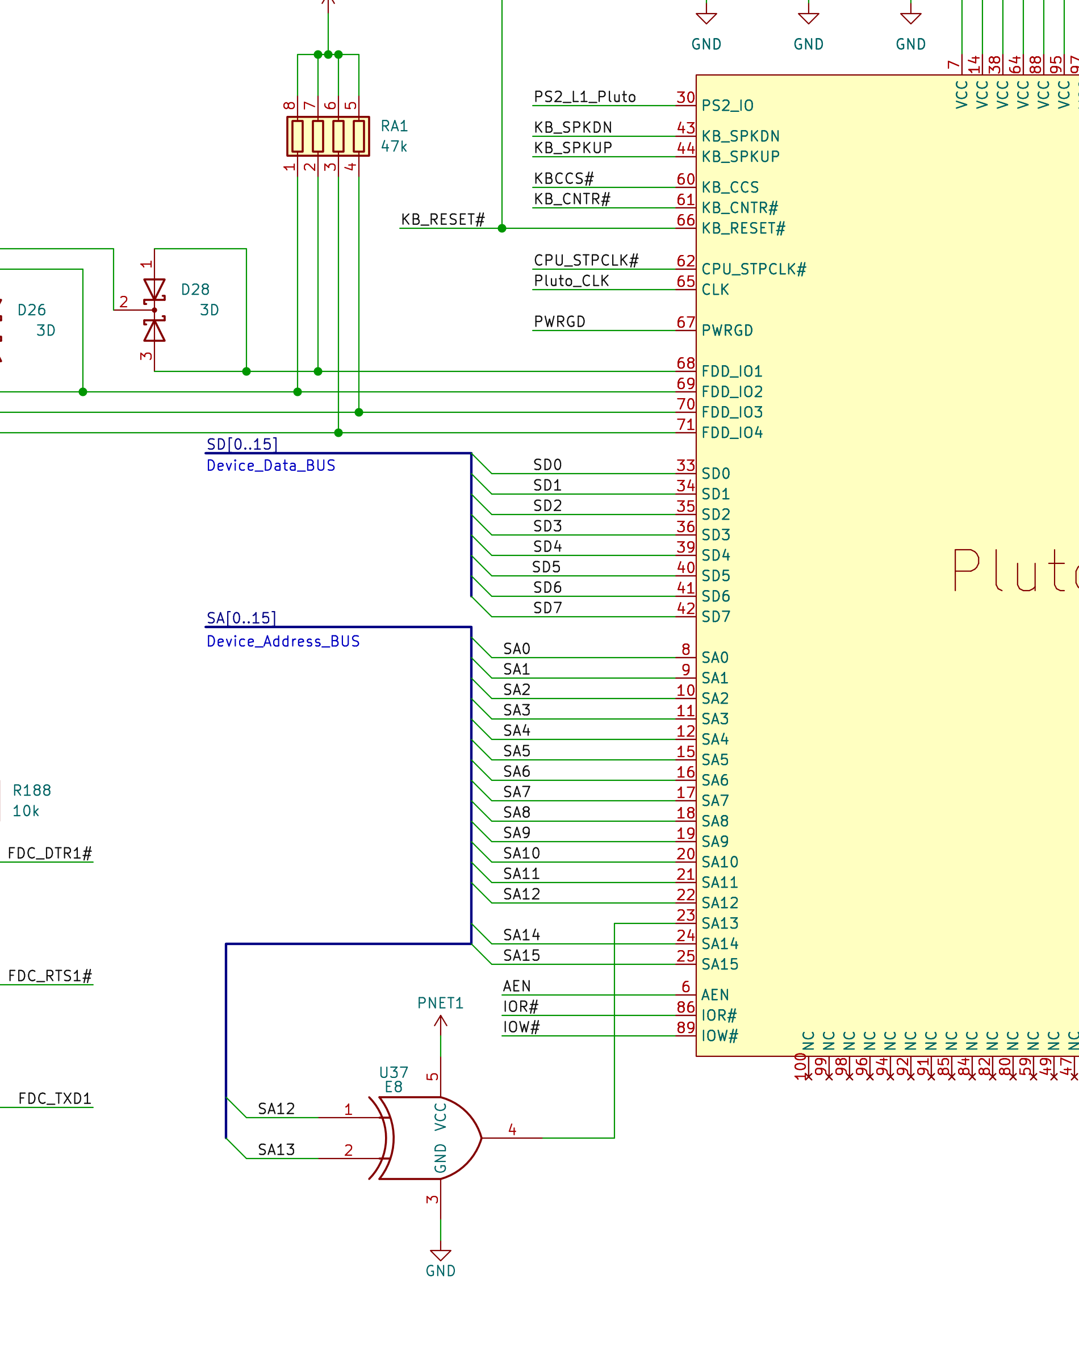
Discovery/Pluto/u35_left.png
