ahmadexp/Open-Source-PC110/Discovery/Pluto/u35_right.png

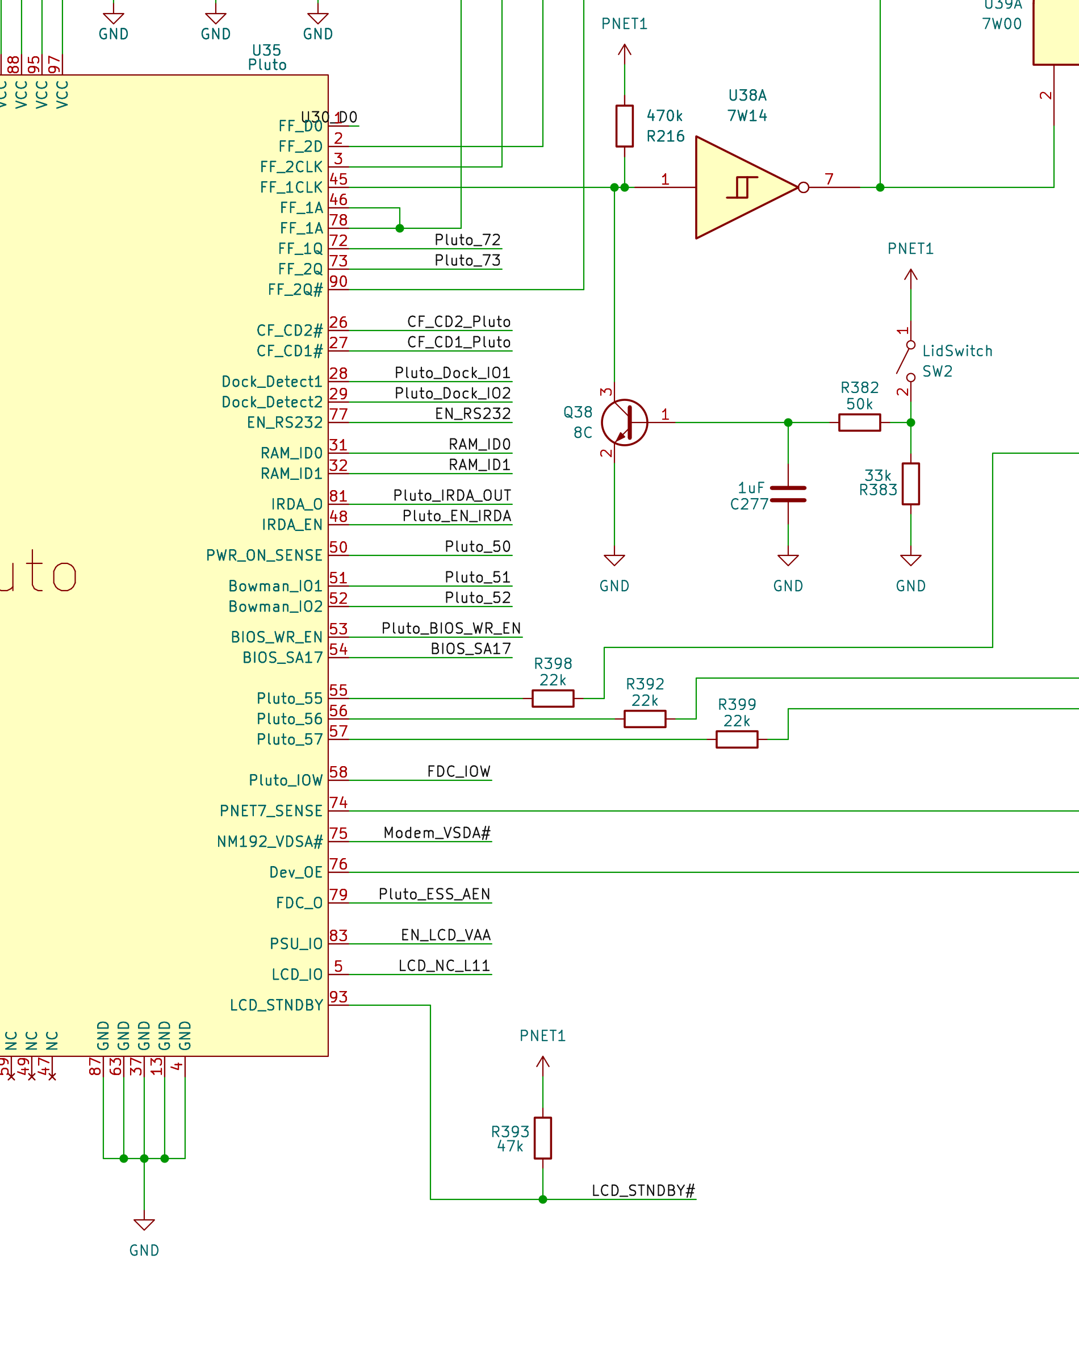
Discovery/Pluto/u35_right.png
