ahmadexp/Open-Source-PC110/Discovery/Pluto/u35_sd.png

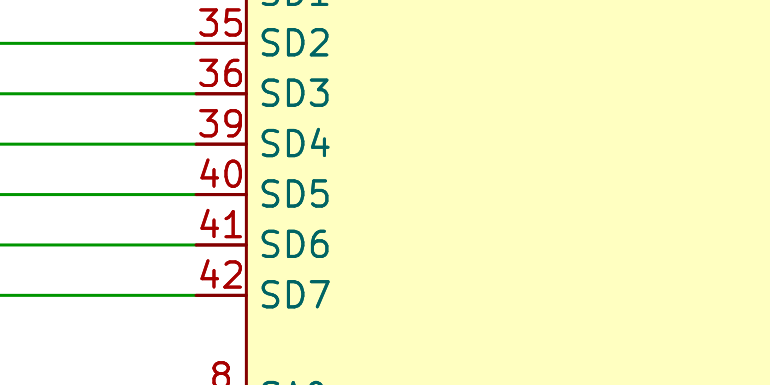
Discovery/Pluto/u35_sd.png
