ahmadexp/Open-Source-PC110/Discovery/Pluto/u35_top.png

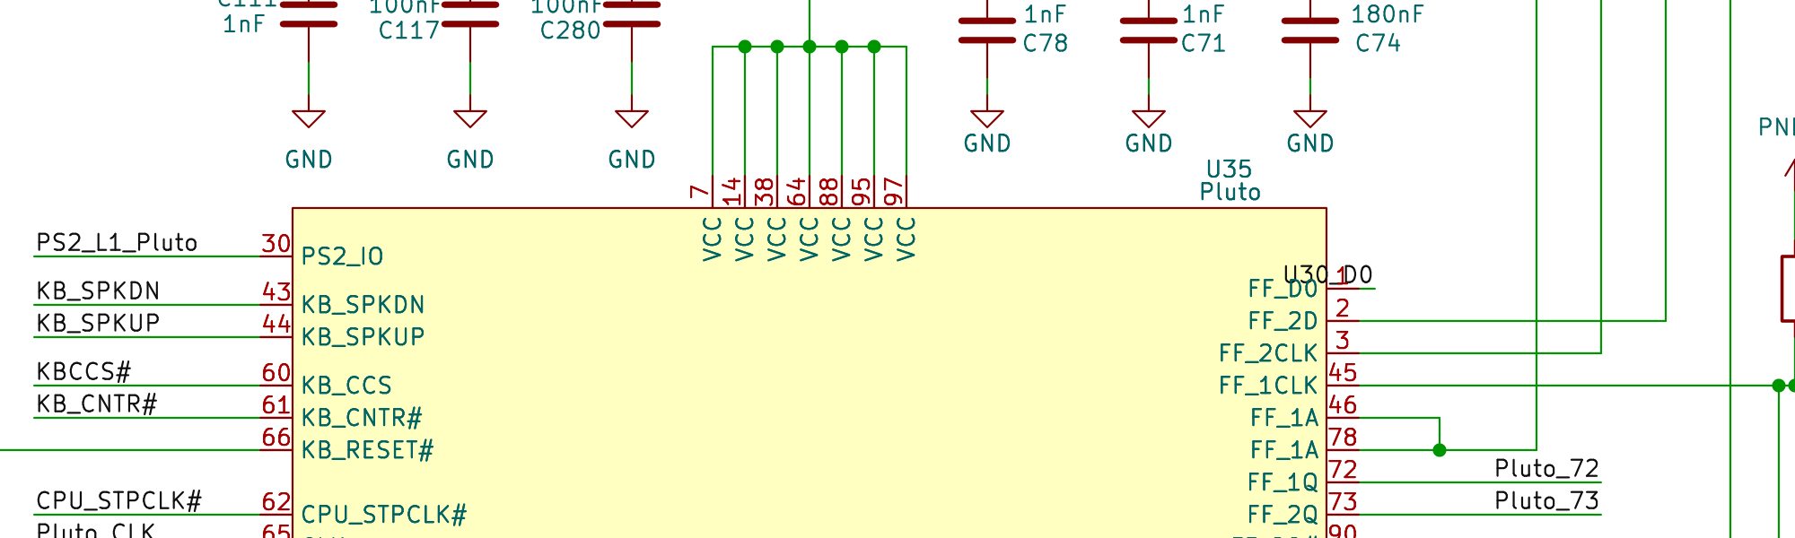
Discovery/Pluto/u35_top.png
