ahmadexp/Open-Source-PC110/Discovery/PSU-MB-M38/J5_bot.png

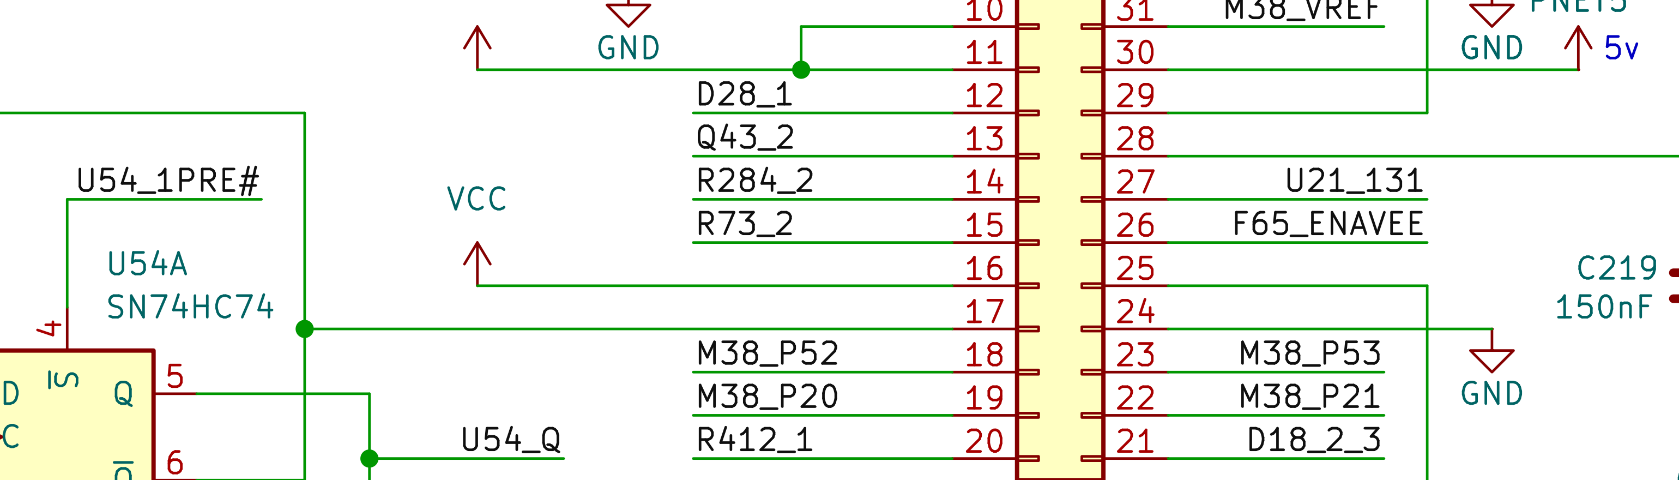
Discovery/PSU-MB-M38/J5_bot.png
