ahmadexp/Open-Source-PC110/Discovery/PSU-MB-M38/J5_top.png

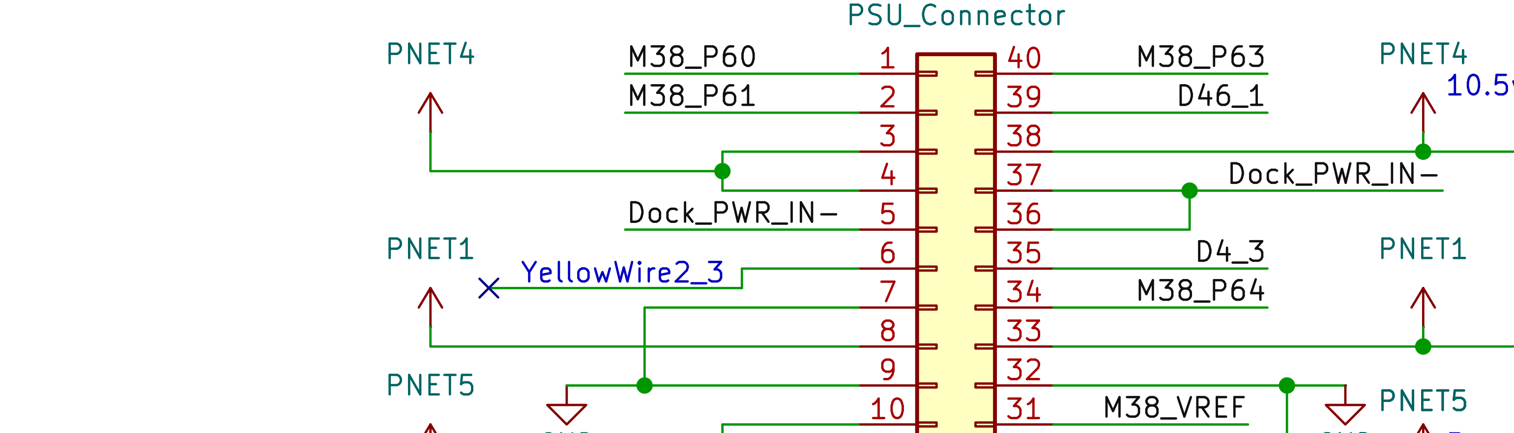
Discovery/PSU-MB-M38/J5_top.png
