ahmadexp/Open-Source-PC110/Discovery/PSU-MB-M38/psu_top.png

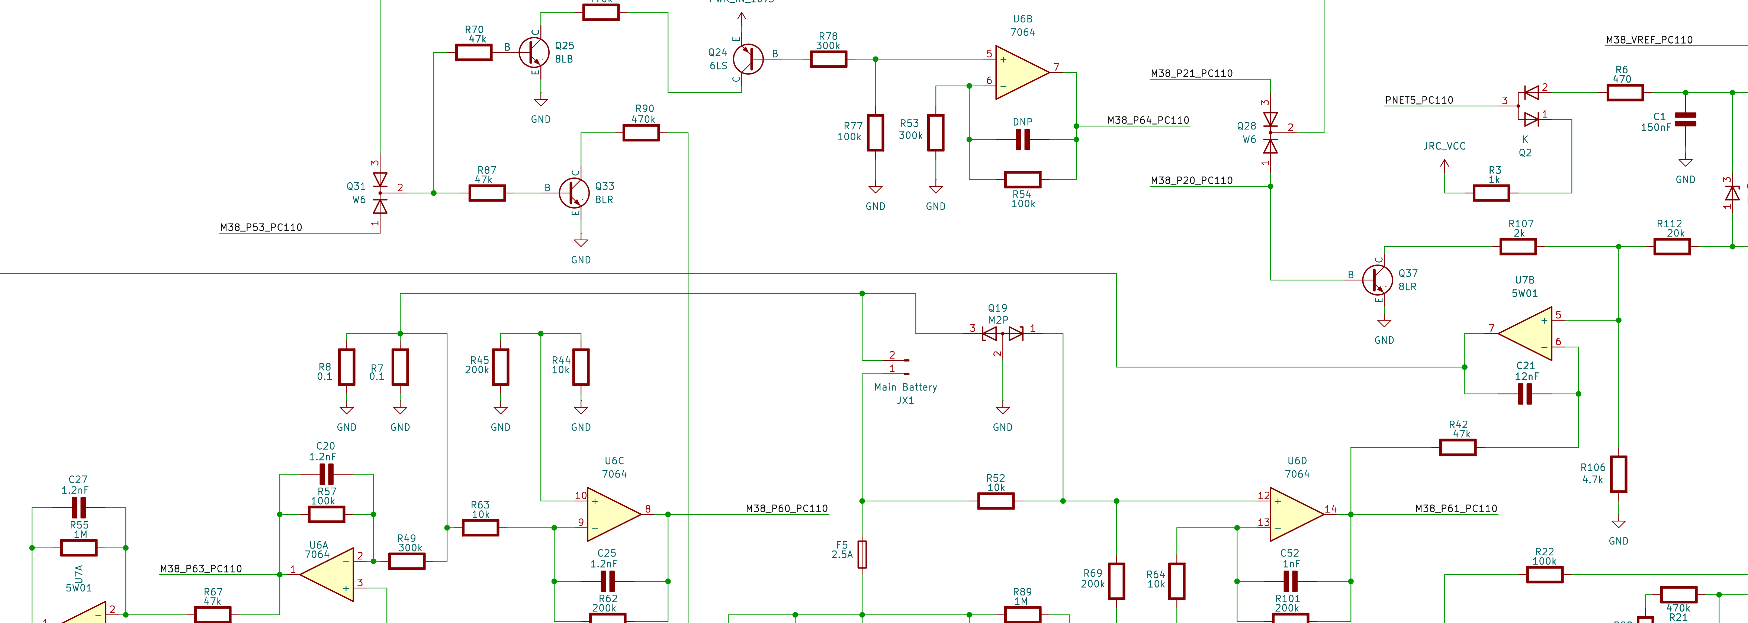
Discovery/PSU-MB-M38/psu_top.png
