ahmadexp/Open-Source-PC110/Components/U61-VL82C420FC5/Decap Indie Chips/04 P82C54.pptx

## P82C54

Prepared by: Applications
04-22-2026

## Slide 2

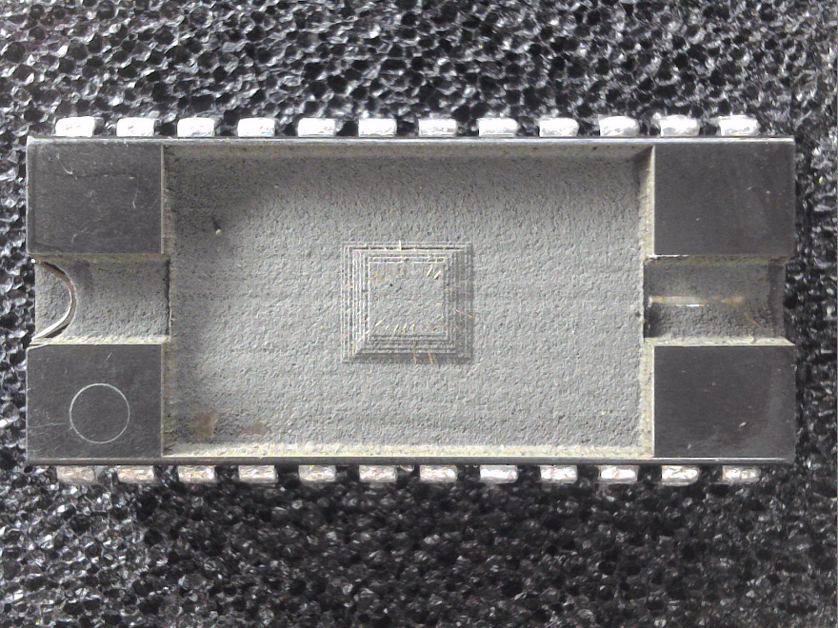
[picture p32: figure]

Post IR DECAP

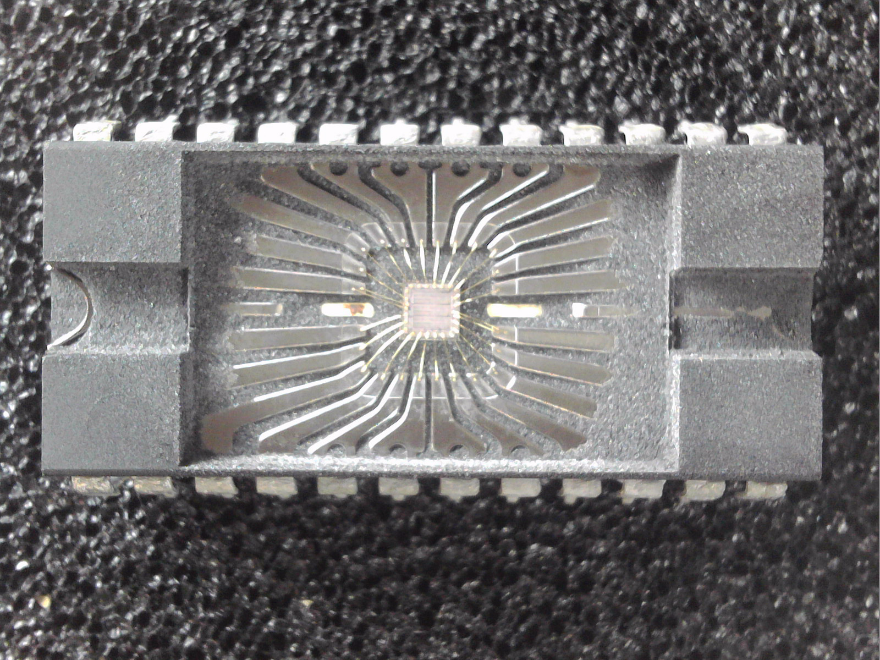
[picture p33: figure]
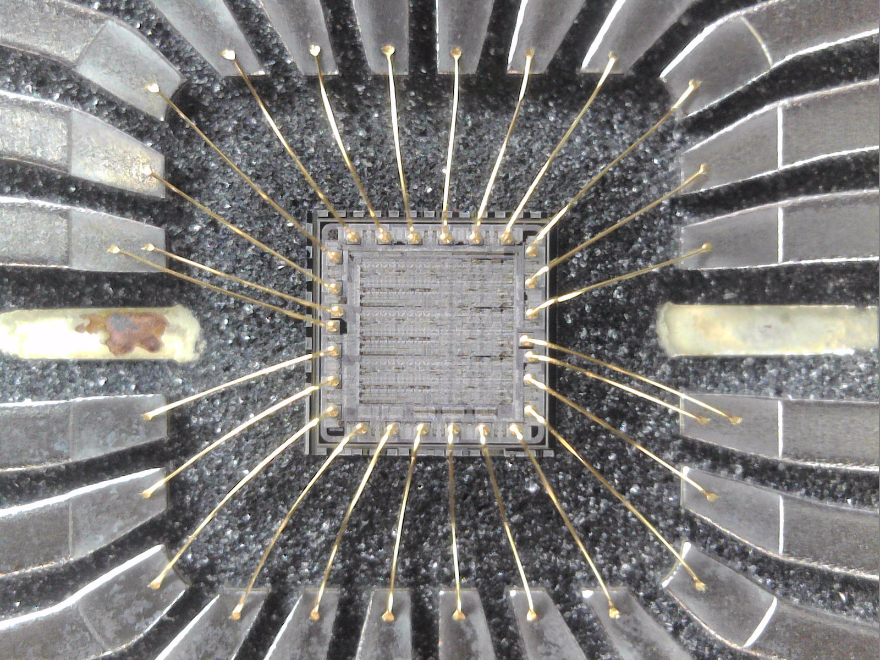
[picture p34: figure]
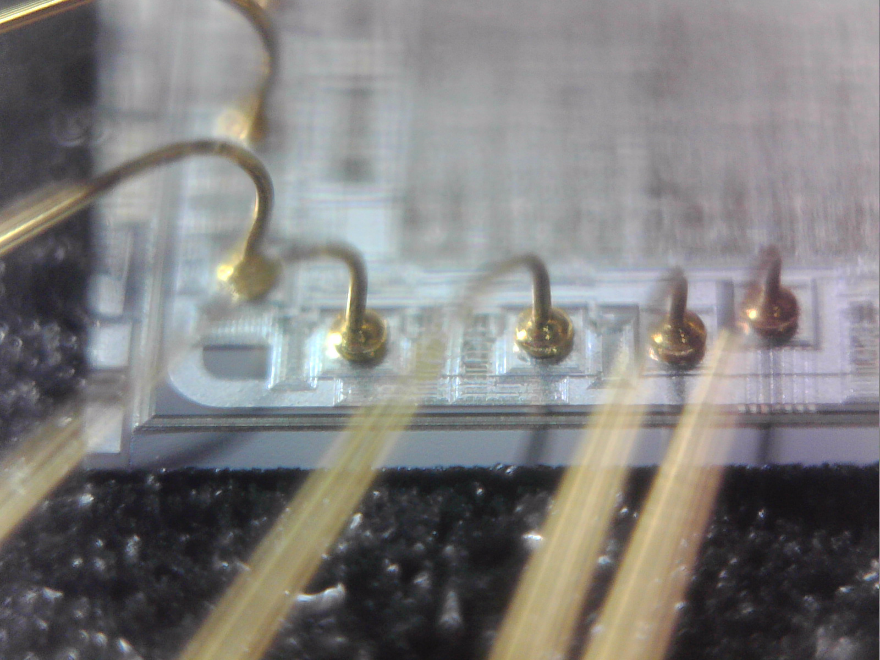
[picture p35: figure]
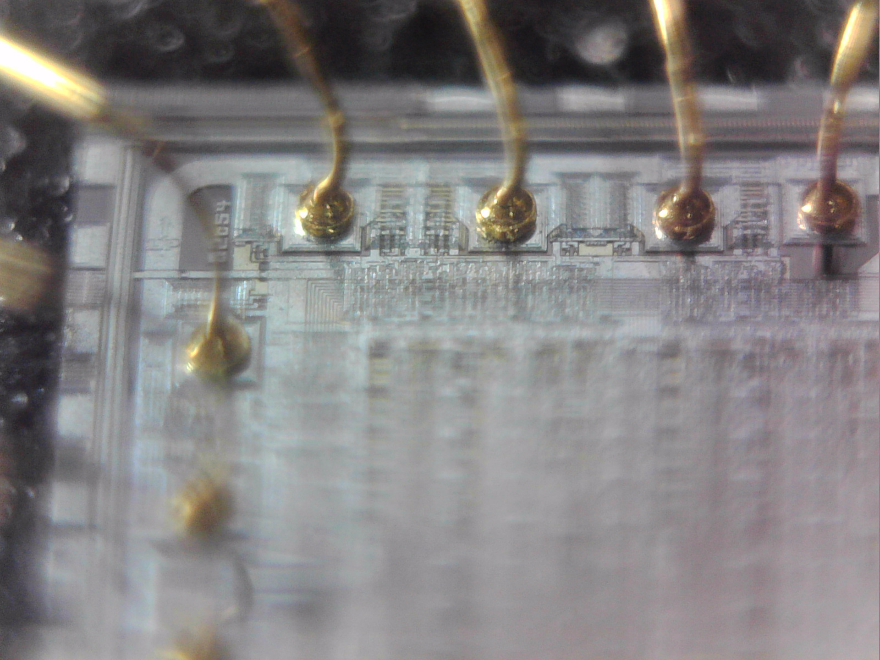
[picture p36: figure]
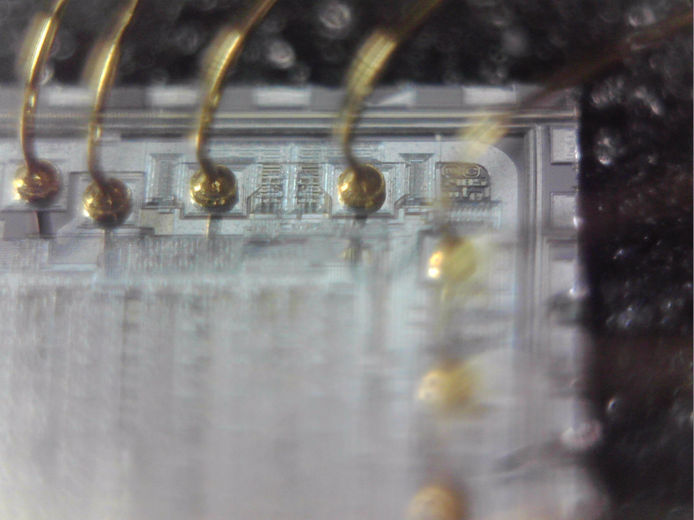
[picture p37: figure]

## Slide 3

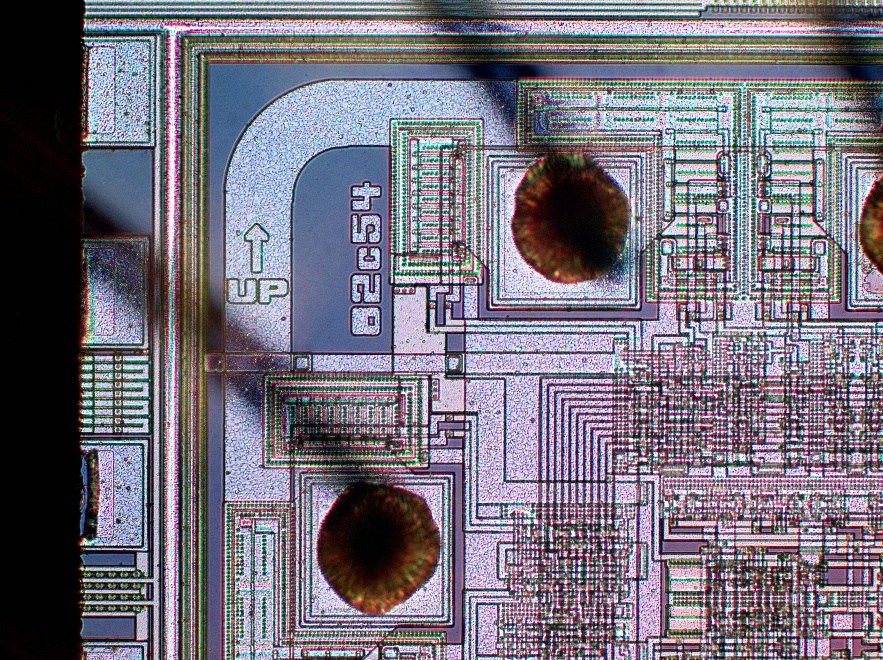
[picture p38: figure]
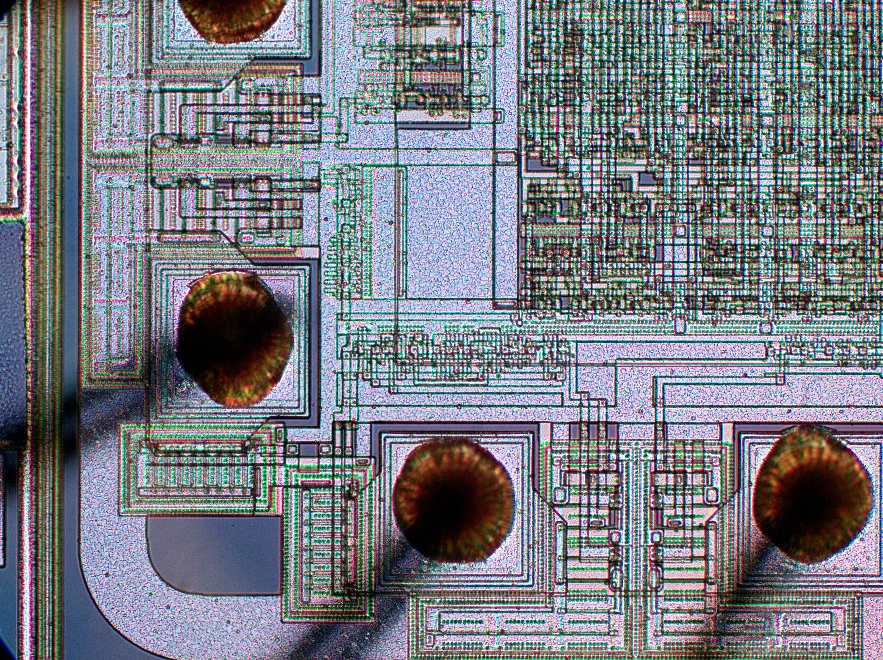
[picture p39: figure]
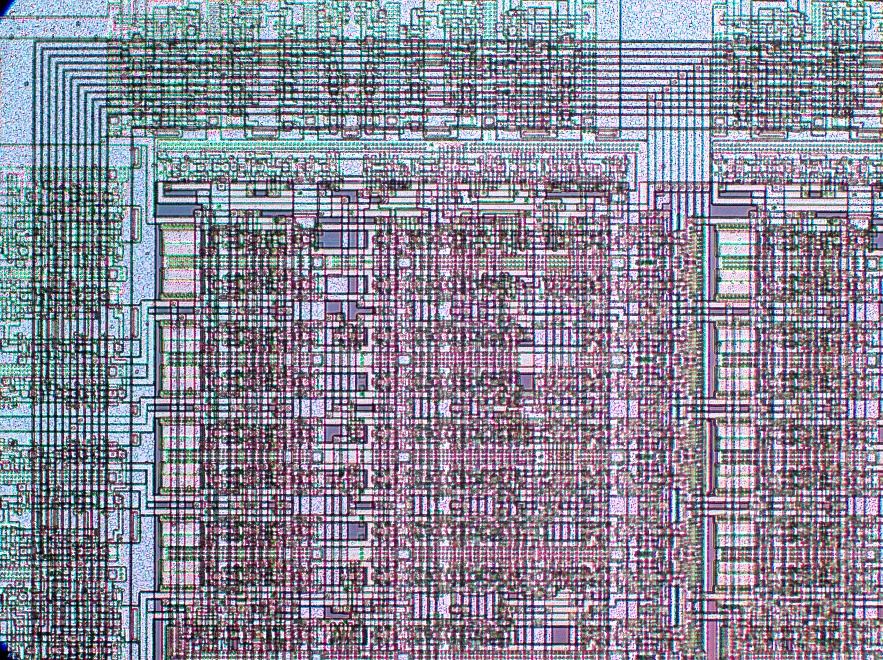
[picture p40: figure]
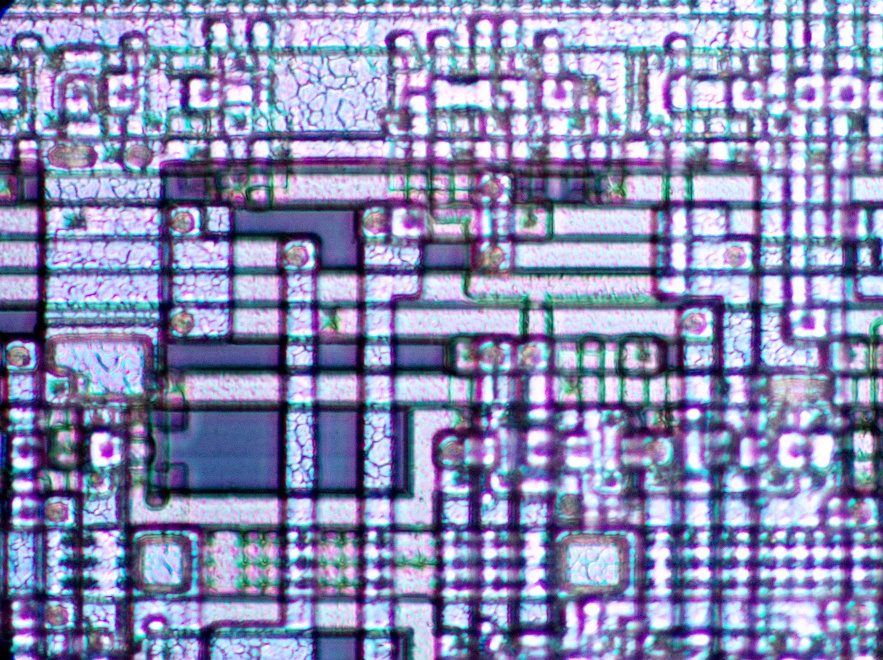
[picture p41: figure]
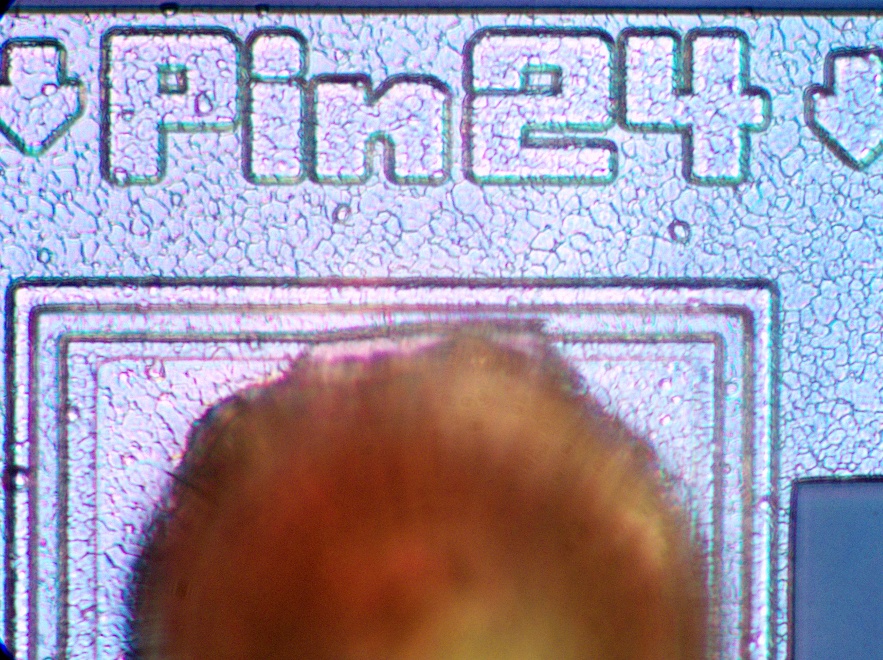
[picture p42: figure]
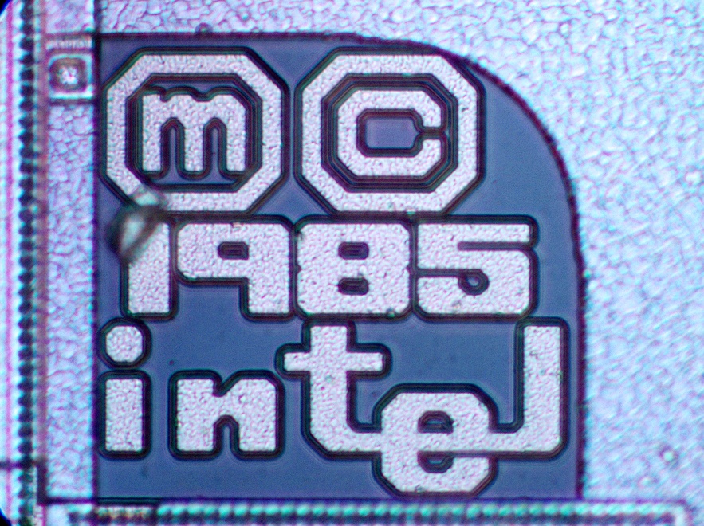
[picture p43: figure]
