ahmadexp/Open-Source-PC110/Components/U61-VL82C420FC5/Decap Indie Chips/03 MC146818AP.pptx

## MC146818AP

Prepared by: Applications
04-22-2026

## Slide 2

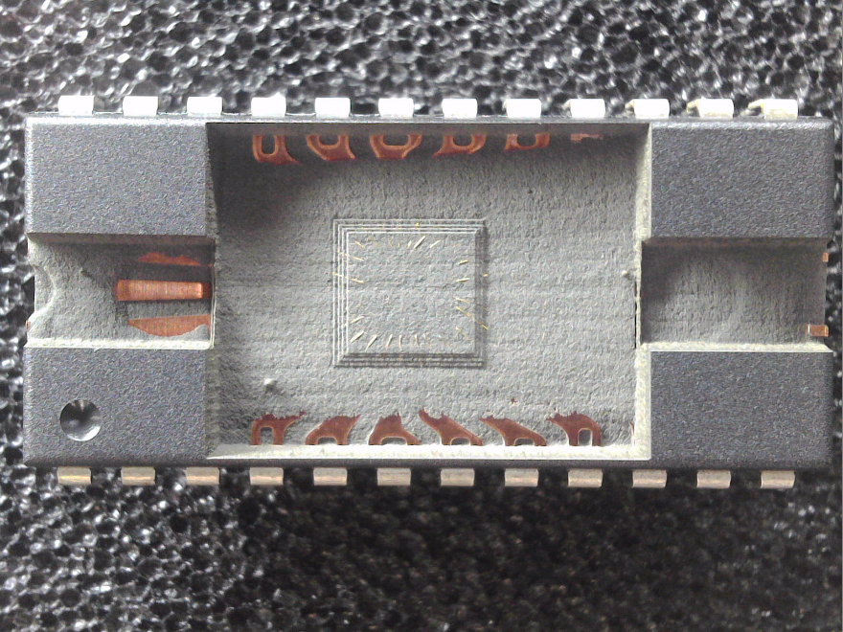
[picture p44: figure]

Post IR DECAP

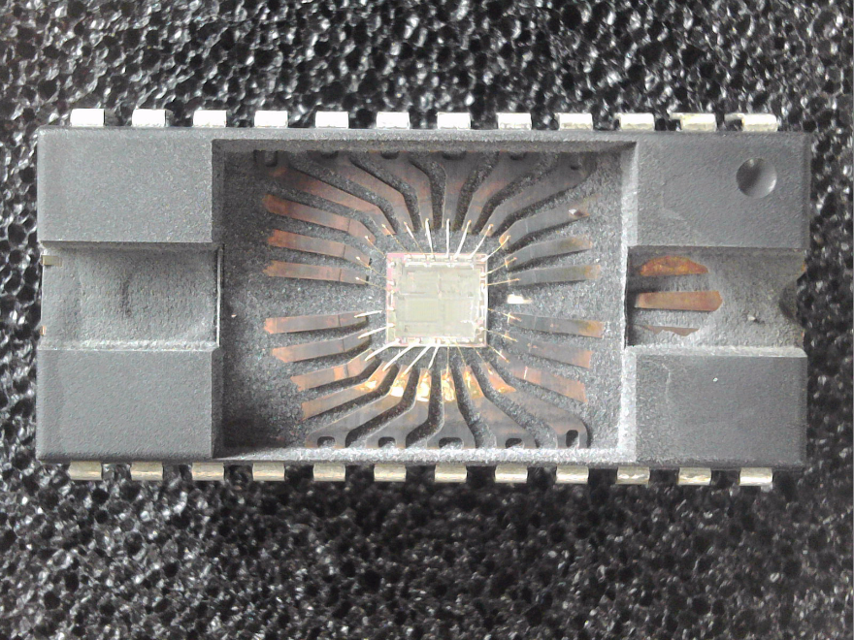
[picture p45: figure]
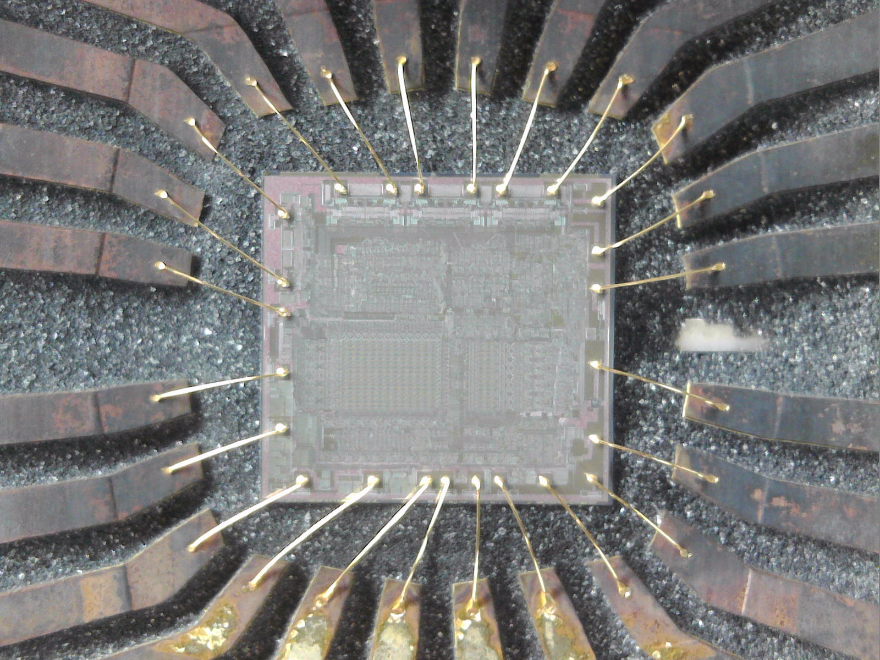
[picture p46: figure]
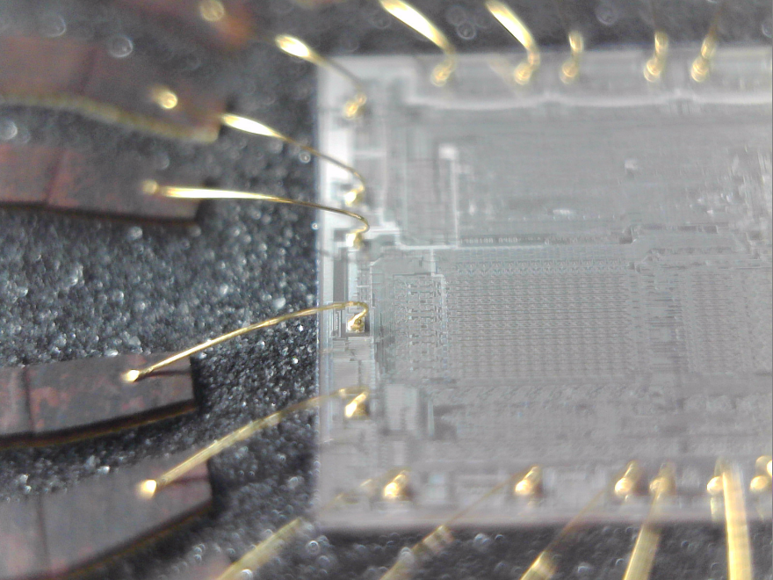
[picture p47: figure]
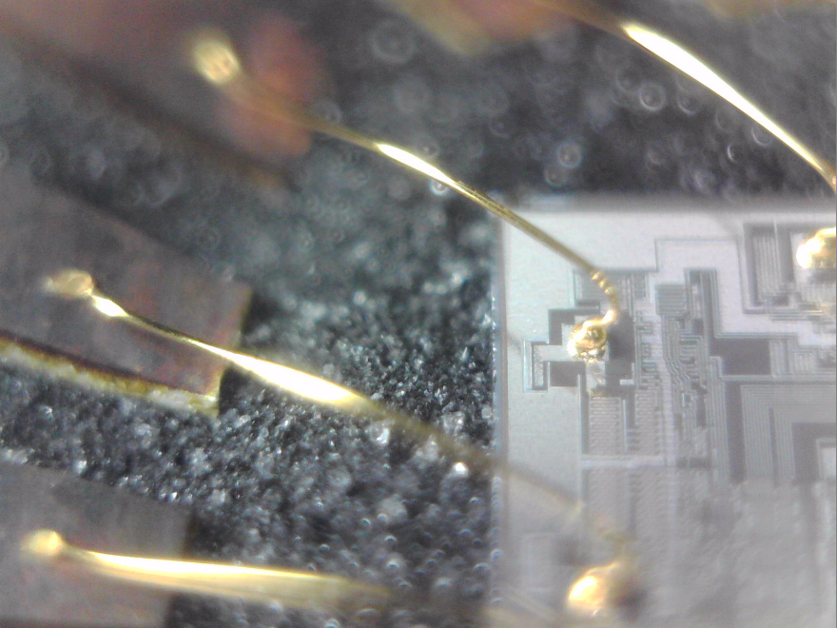
[picture p48: figure]
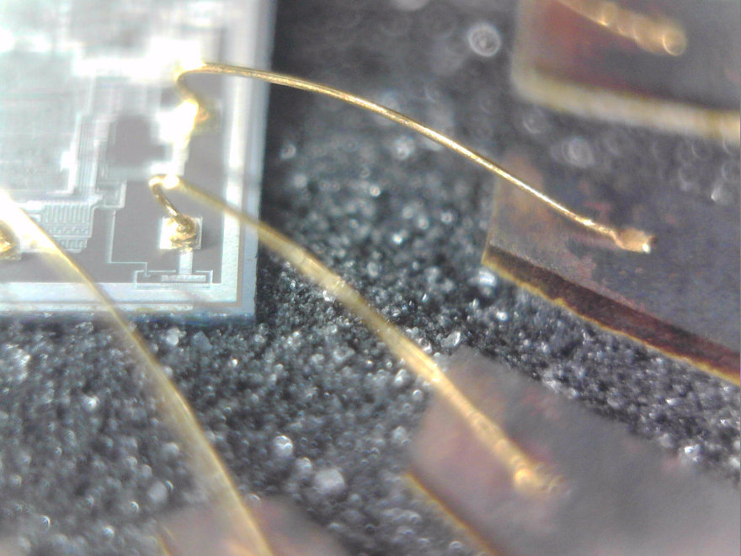
[picture p49: figure]

## Slide 3

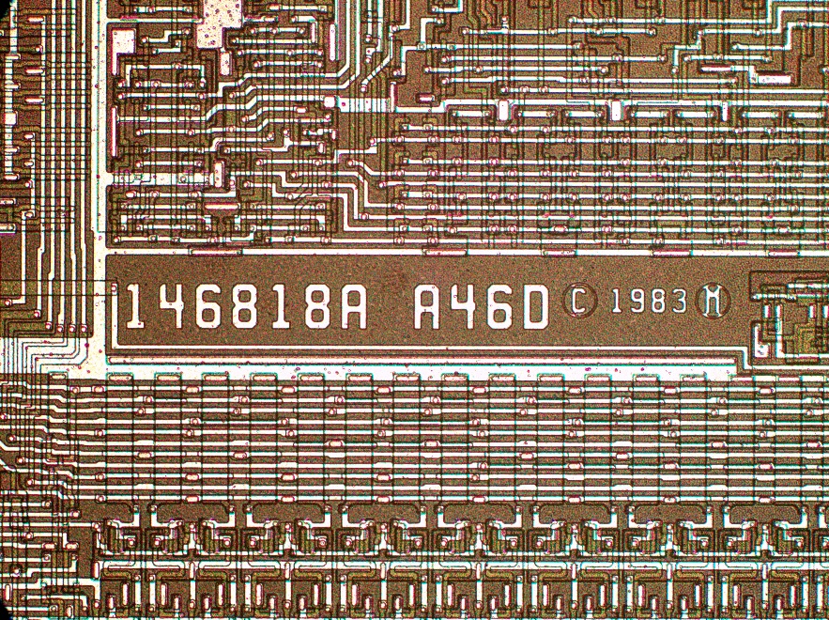
[picture p50: figure]
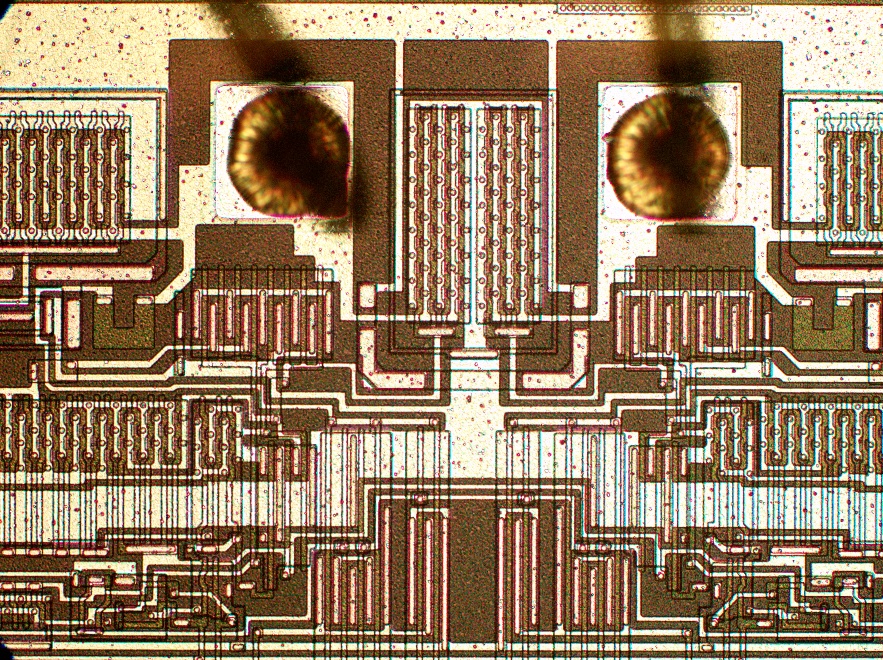
[picture p51: figure]
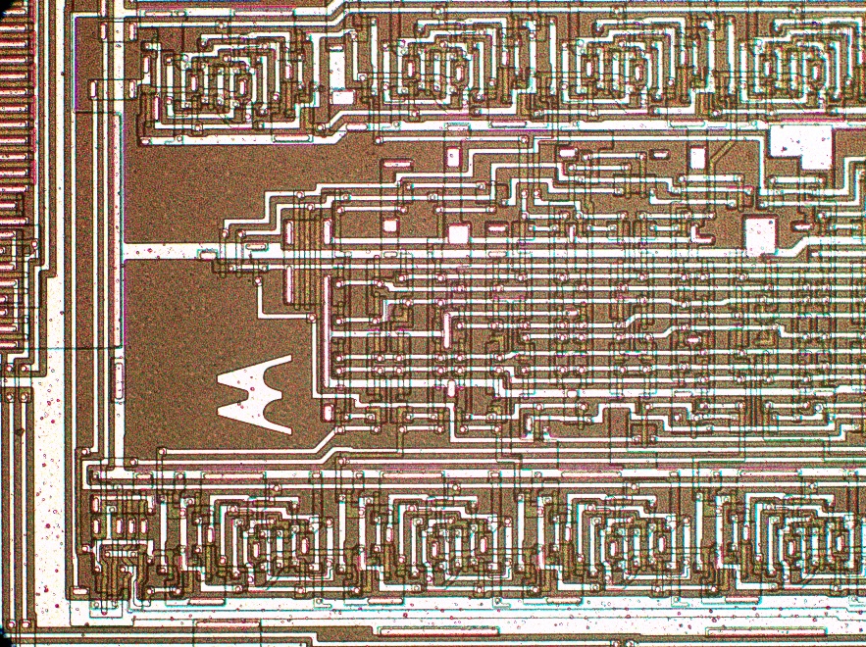
[picture p52: figure]
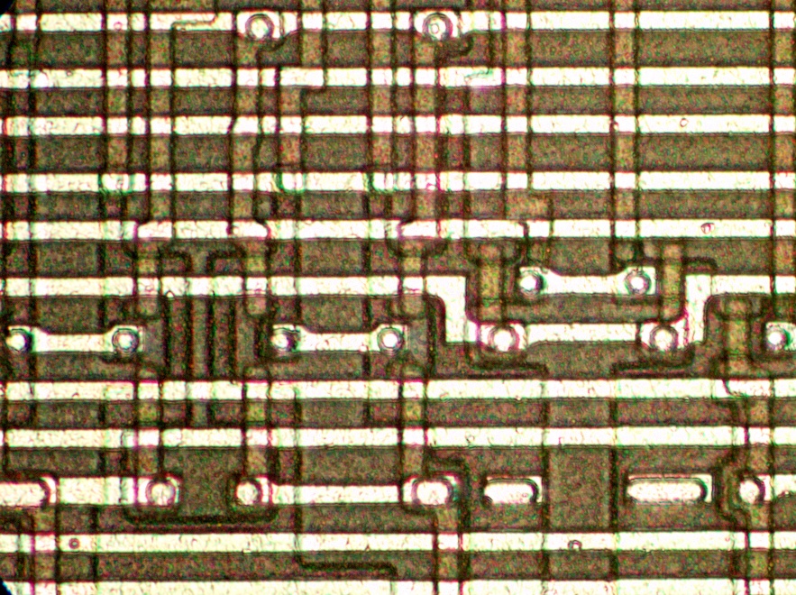
[picture p53: figure]
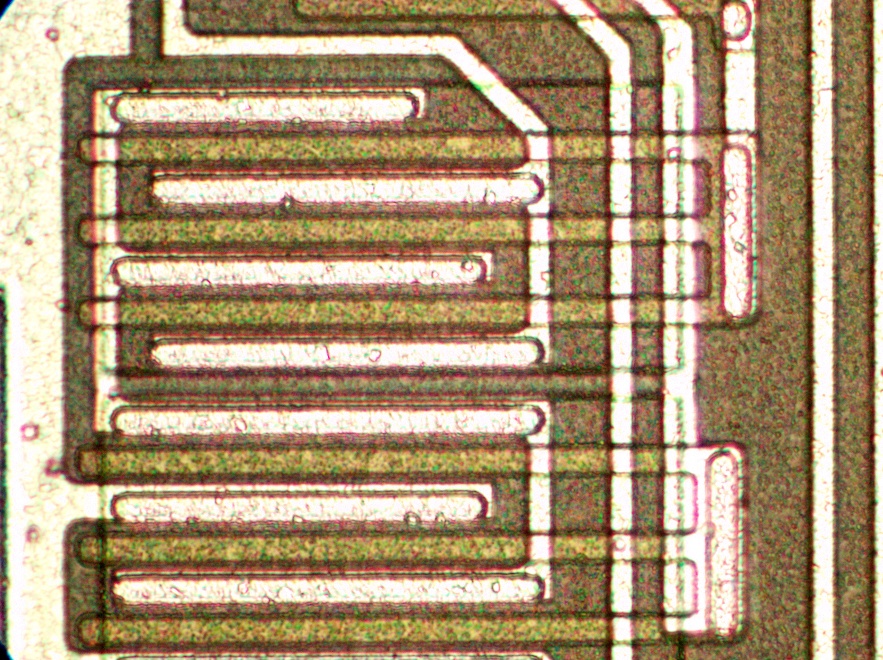
[picture p54: figure]
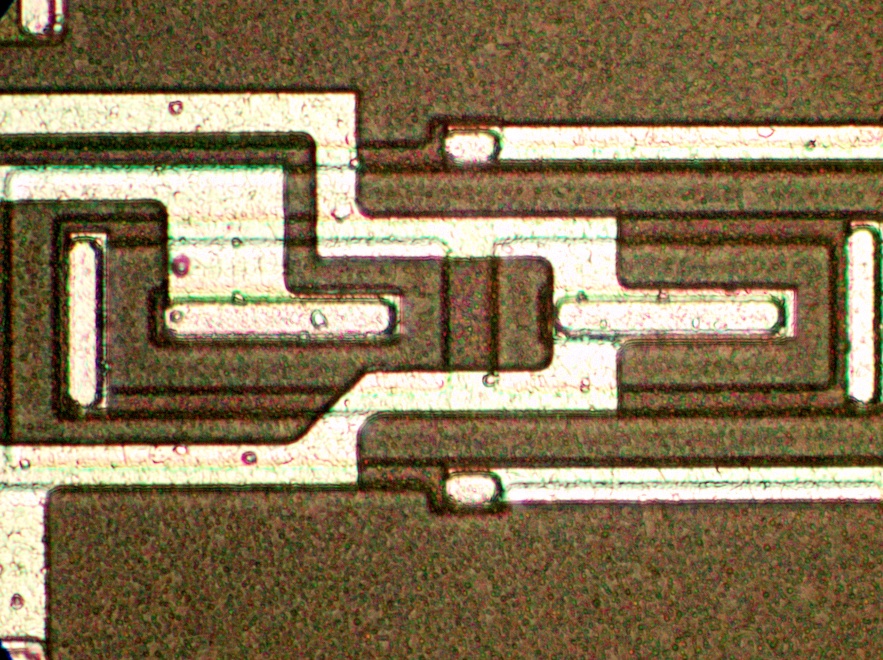
[picture p55: figure]
