ahmadexp/Open-Source-PC110/Components/U61-VL82C420FC5/Decap Indie Chips/02 P82C69A-2.pptx

## P82C69A-2

Prepared by: Applications
04-17-2026

## Slide 2

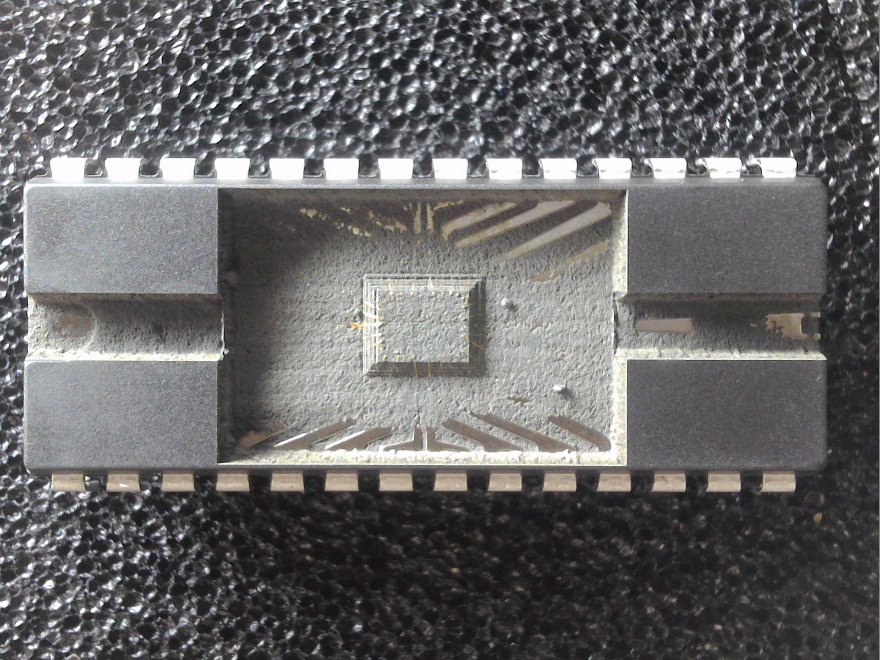
[picture p56: figure]

Post IR DECAP

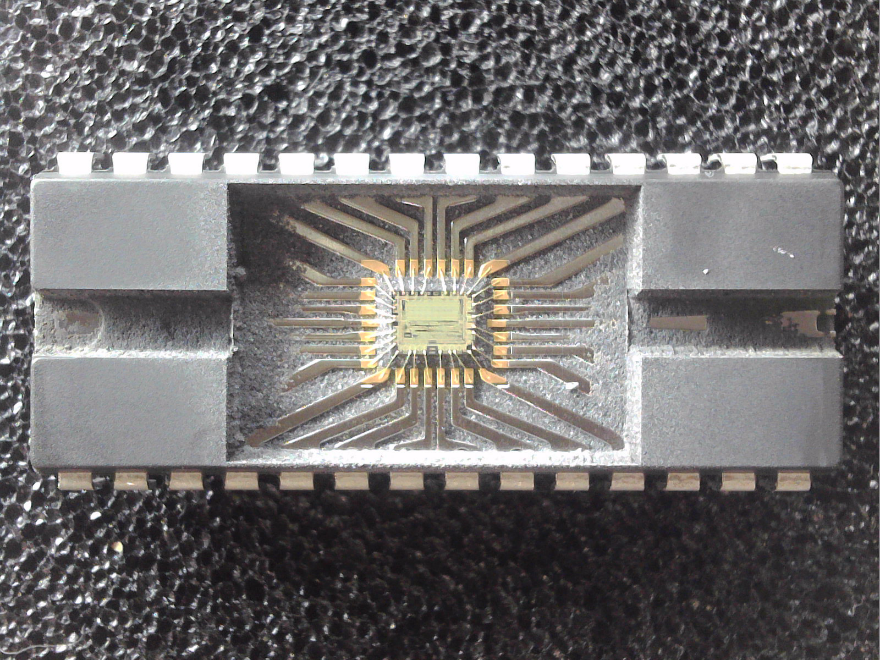
[picture p57: figure]
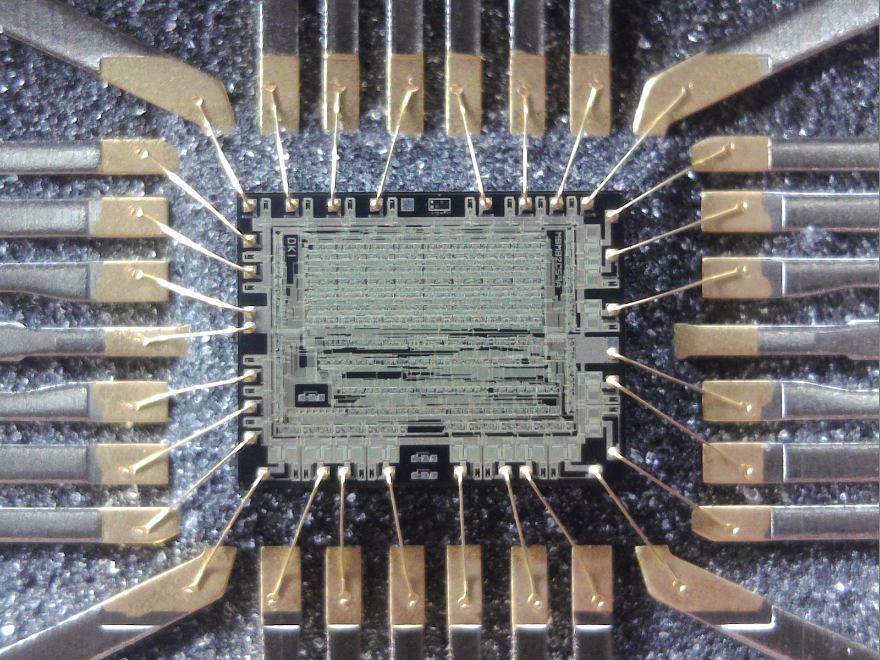
[picture p58: figure]
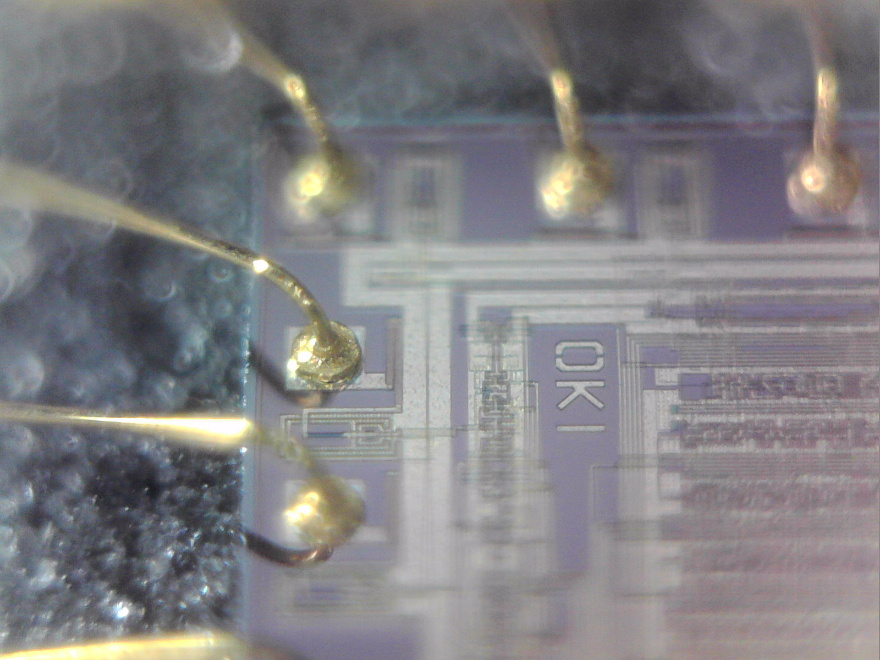
[picture p59: figure]
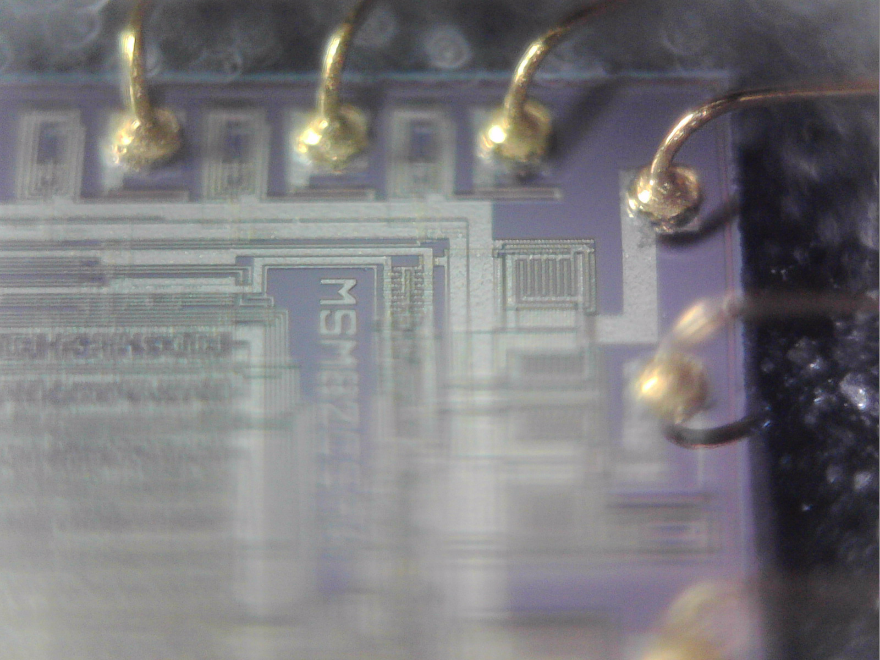
[picture p60: figure]
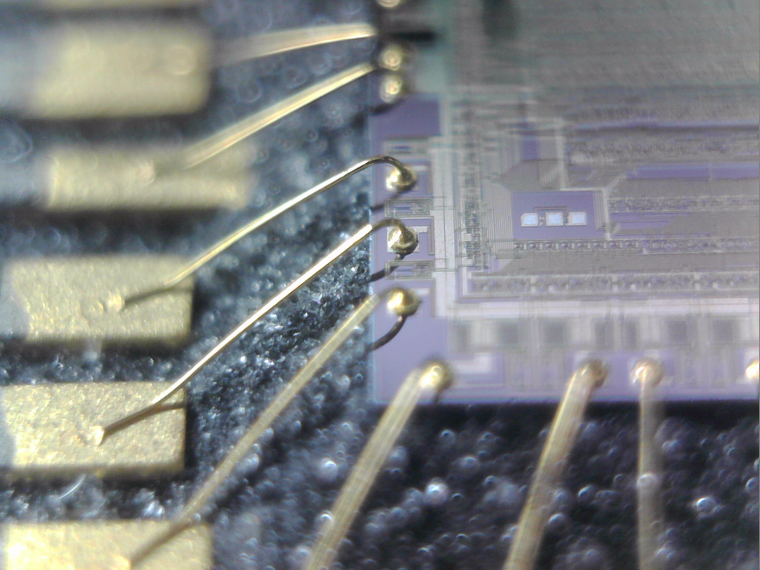
[picture p61: figure]

## Slide 3

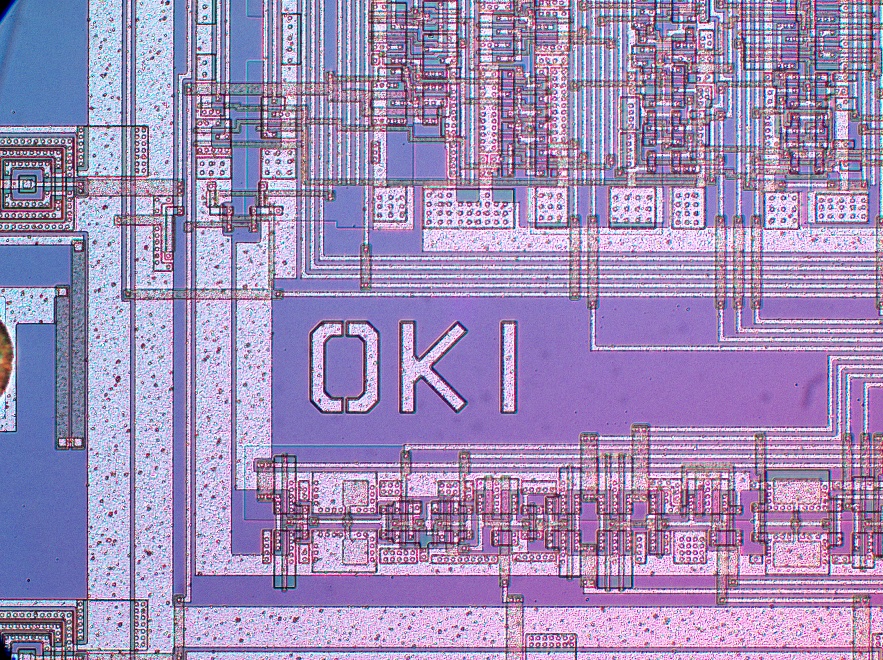
[picture p62: figure]
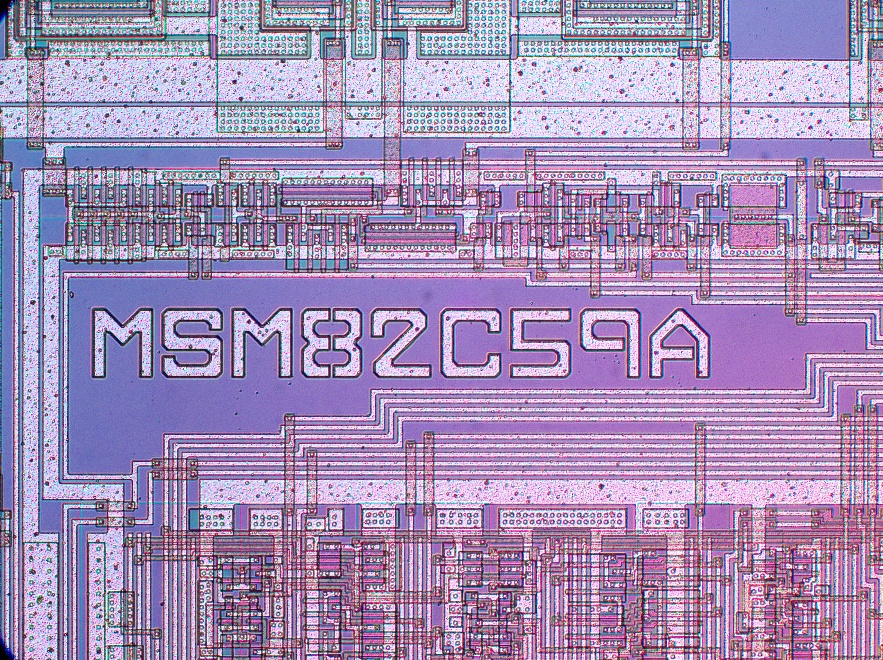
[picture p63: figure]
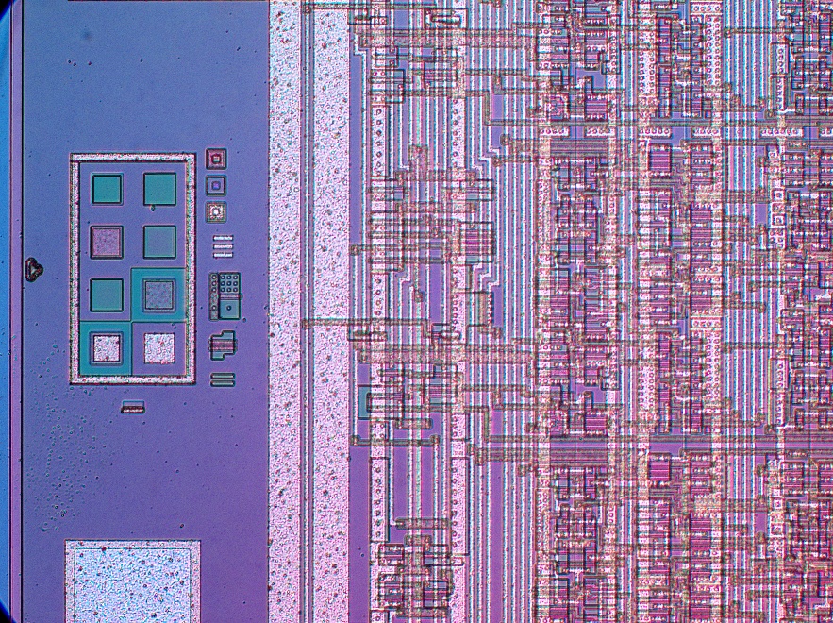
[picture p64: figure]
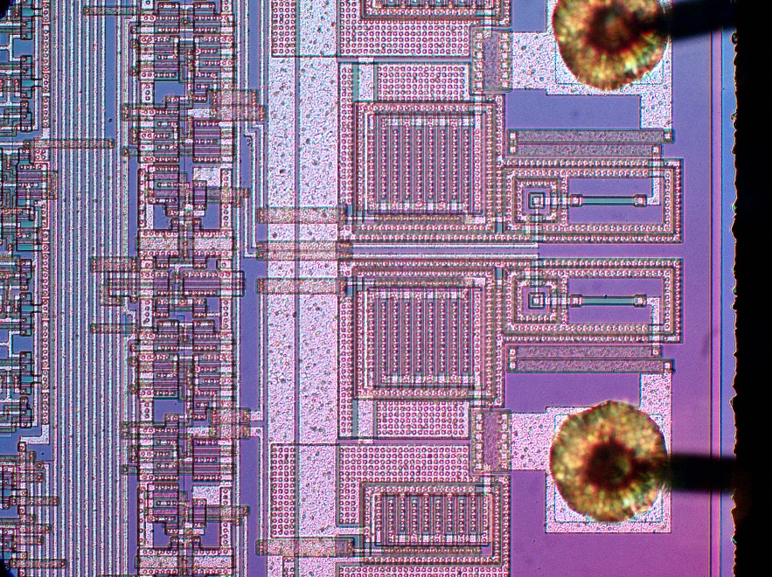
[picture p65: figure]
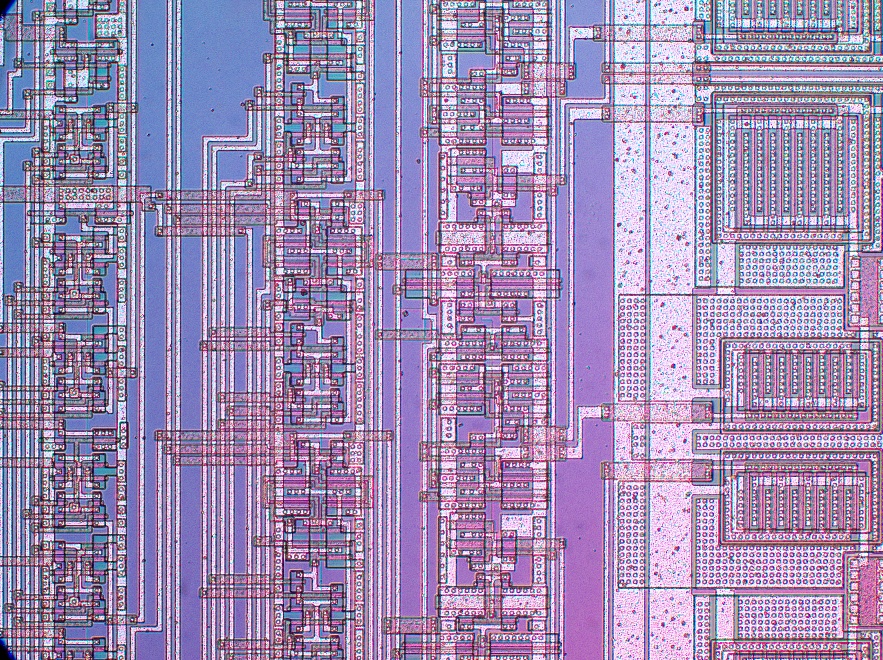
[picture p66: figure]
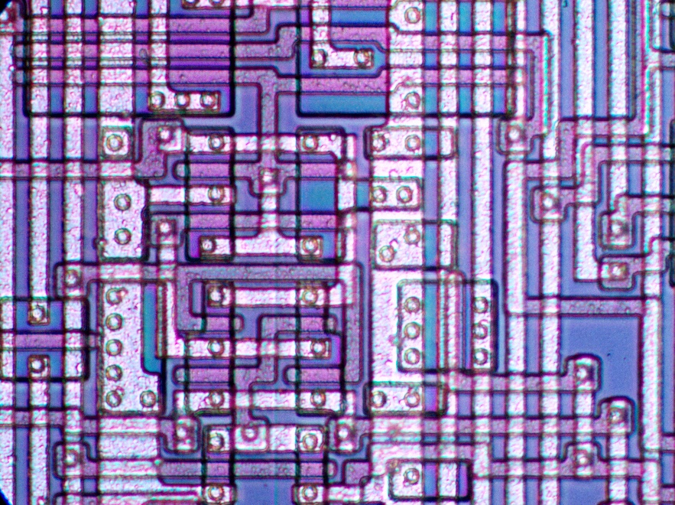
[picture p67: figure]
