ahmadexp/Open-Source-PC110/Components/U61-VL82C420FC5/Decap Indie Chips/01 P82C37A-5.pptx

## P82C37A-5

Prepared by: Applications
04-16-2026

## Slide 2

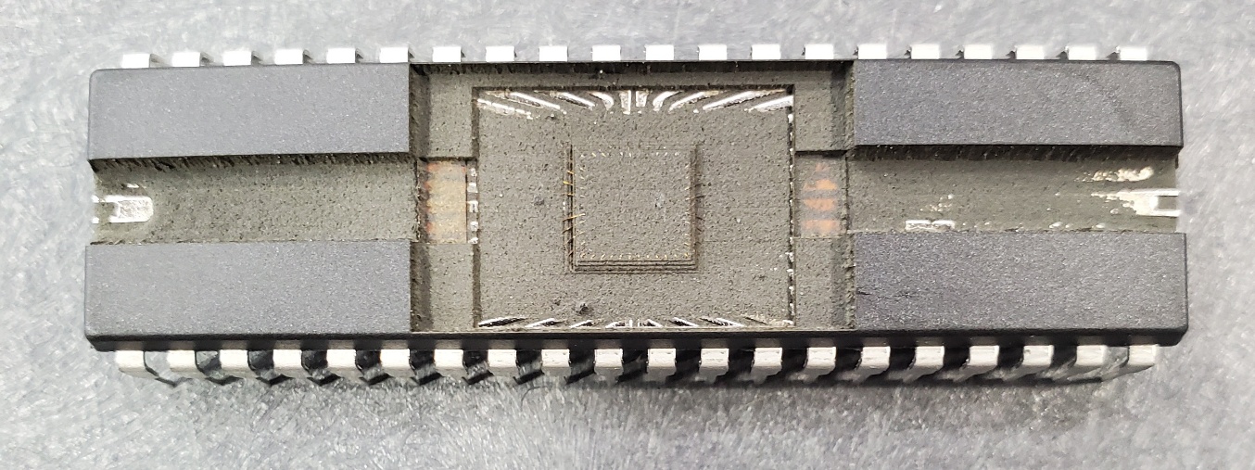
[picture p68: figure]

Post IR DECAP

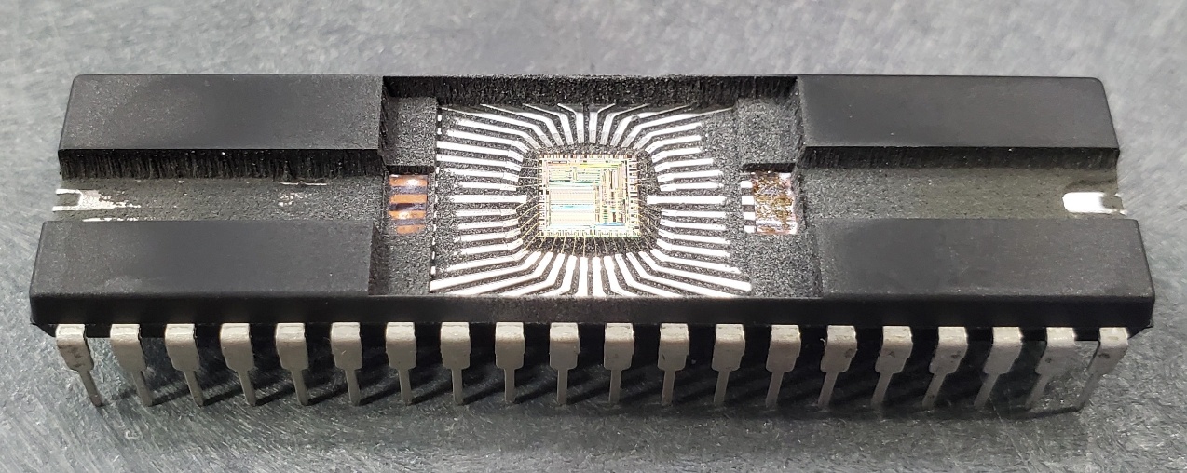
[picture p69: figure]
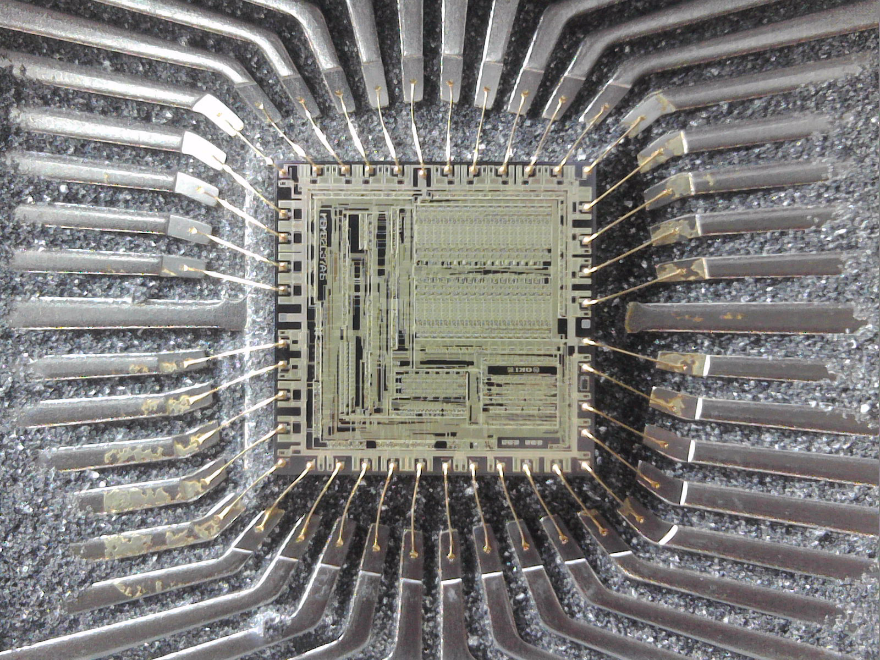
[picture p70: figure]
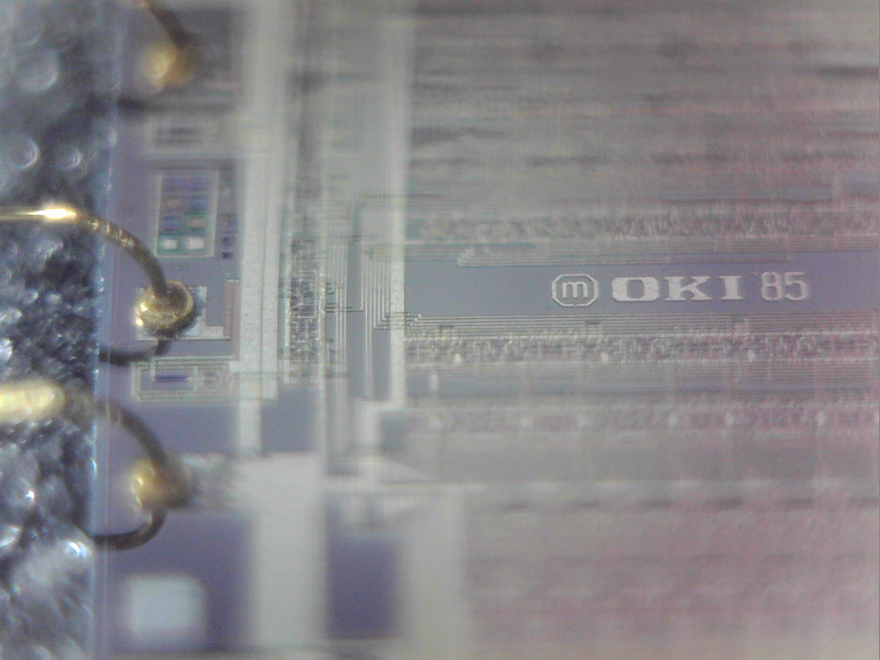
[picture p71: figure]
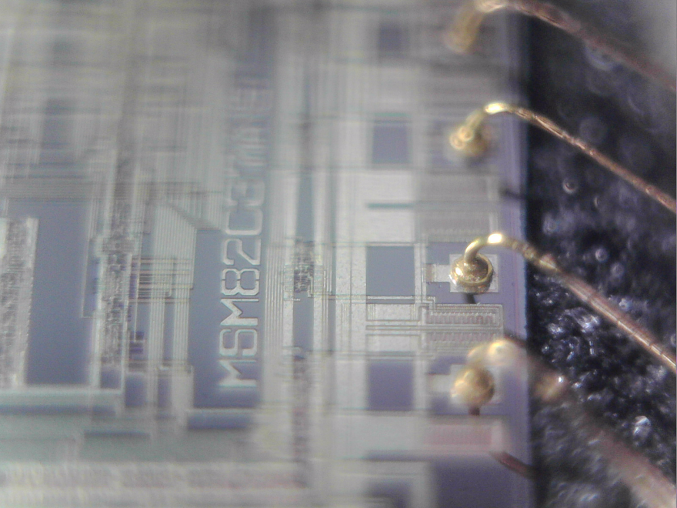
[picture p72: figure]

## Slide 3

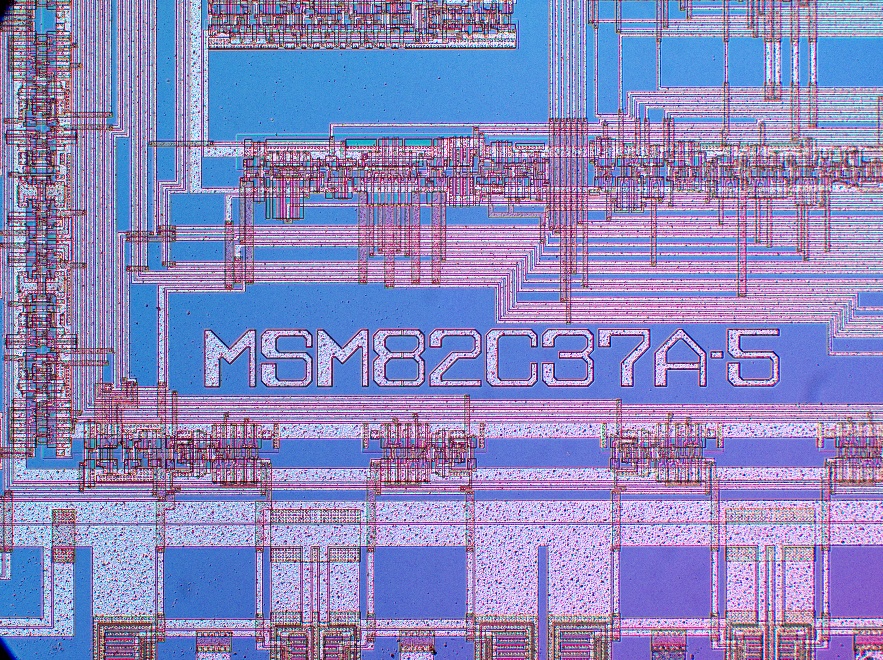
[picture p73: figure]
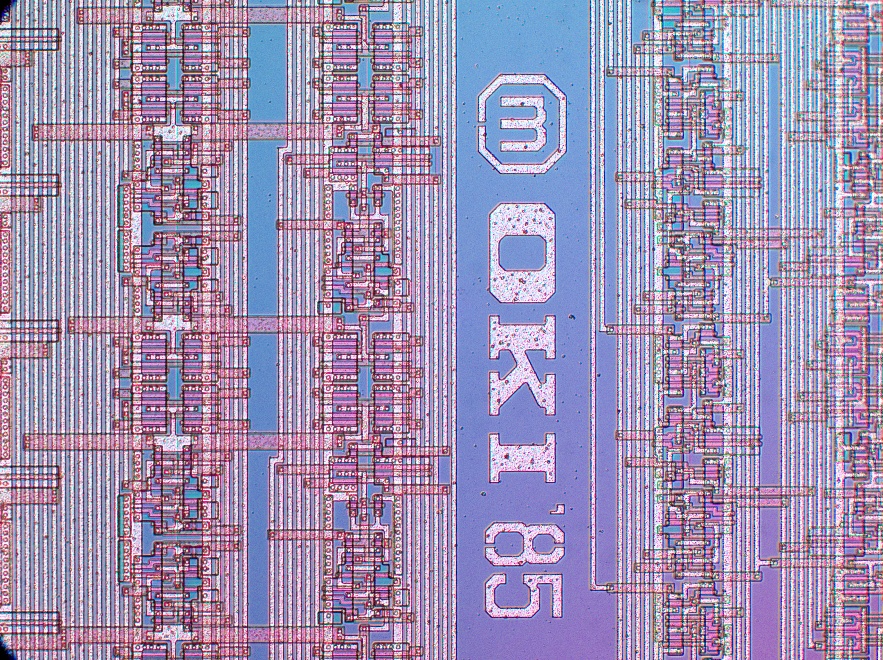
[picture p74: figure]
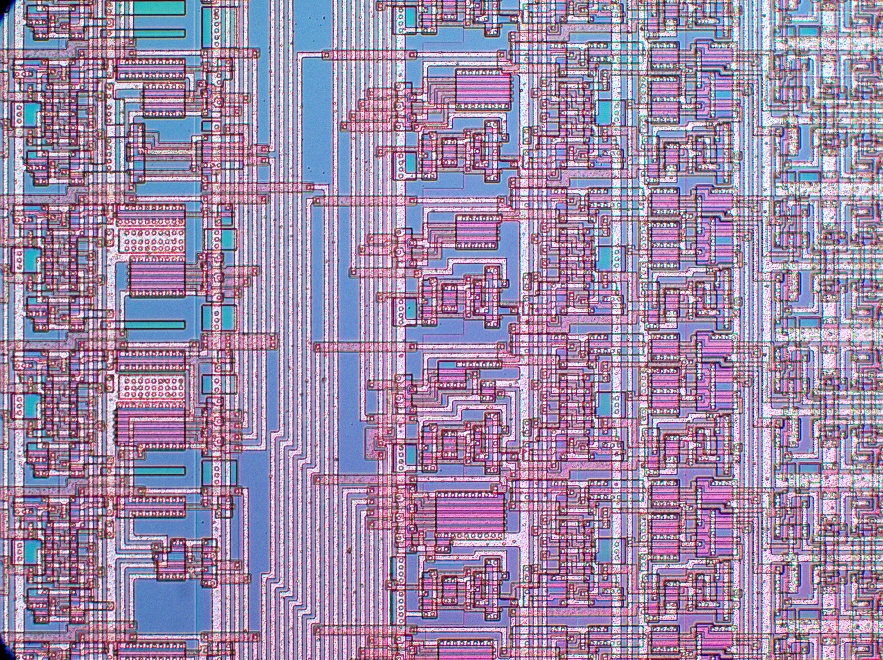
[picture p75: figure]
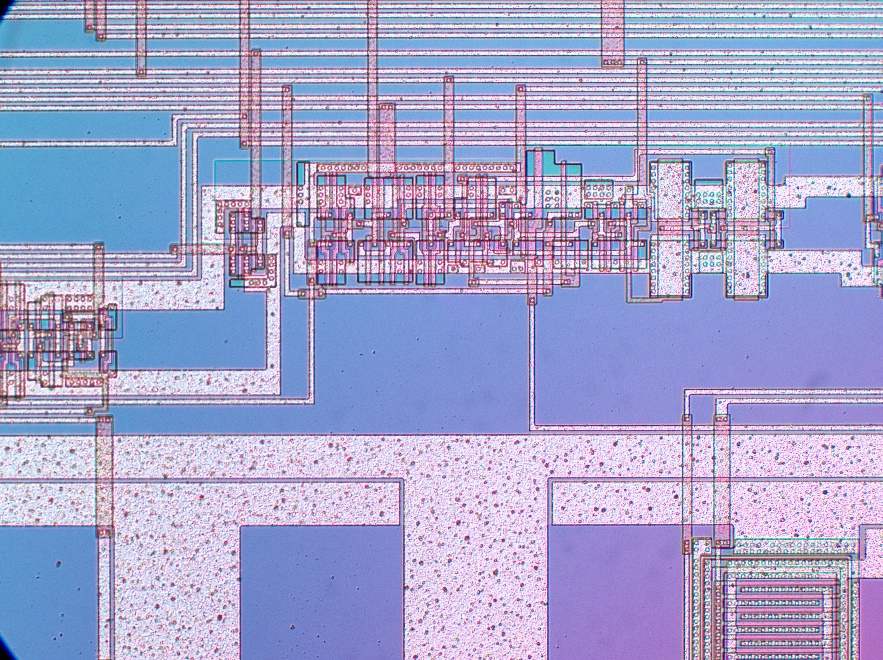
[picture p76: figure]
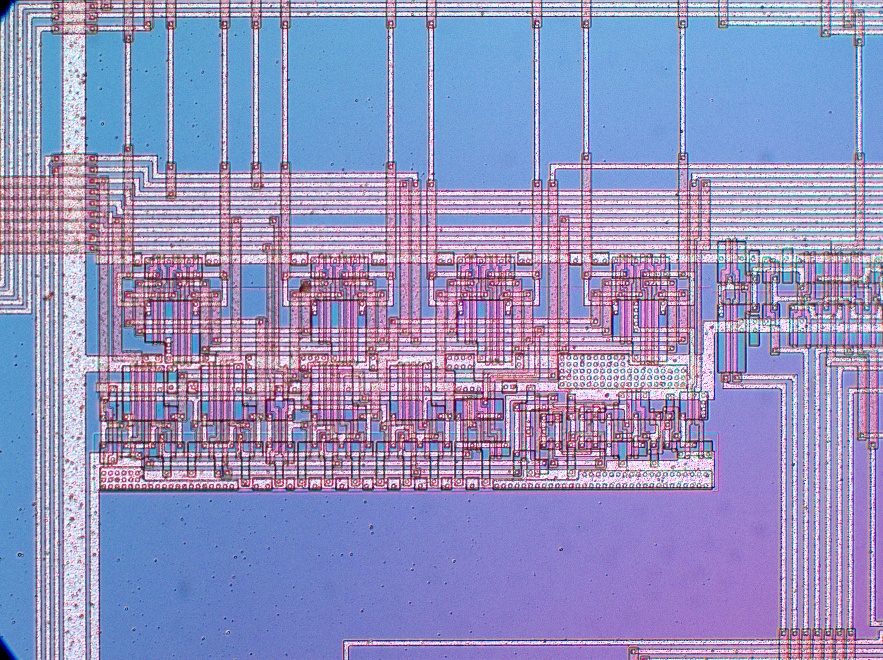
[picture p77: figure]
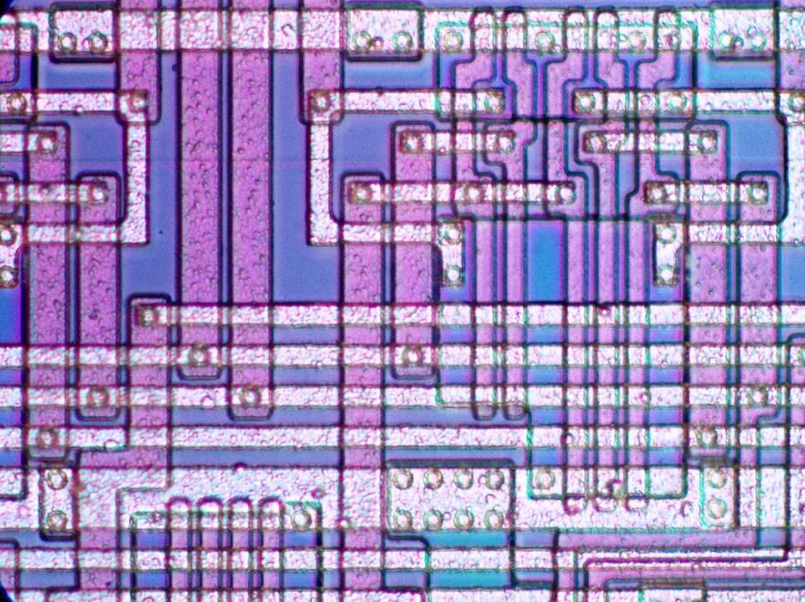
[picture p78: figure]
