ahmadexp/Open-Source-PC110/Components/U61-VL82C420FC5/VL82C018 alternative/screen.png

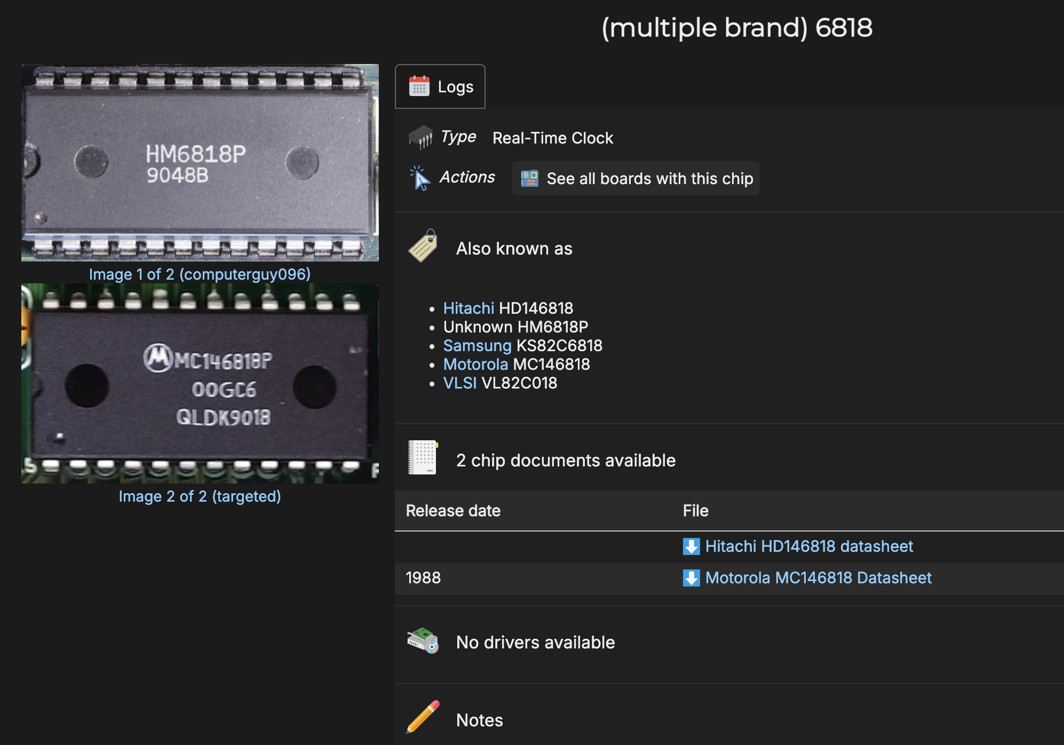
Components/U61-VL82C420FC5/VL82C018 alternative/screen.png
