ahmadexp/Open-Source-PC110/Software/COMrade/src/types.h

/* types.h - minimal fixed-width integer types (serial agent; no mTCP). */
#ifndef TYPES_H
#define TYPES_H

typedef unsigned char  uint8_t;
typedef signed   char  int8_t;
typedef unsigned short uint16_t;
typedef signed   short int16_t;
typedef unsigned long  uint32_t;
typedef signed   long  int32_t;

#endif
